proggi64/fischertechnik-box-foundation/Documentation/de/Base/getStrutDepth.md

# getStrutDepth

Funktion: Liefert die Breite einer Strebe.

## Use
```
use <../Base/Constants.scad>
```

## Syntax
```
getStrutDepth();
```

## Rückgabewert
Breite einer Strebe (8 mm).
