proggi64/fischertechnik-box-foundation/Documentation/de/Base/getStrutOuterTolerance.md

# getStrutOuterTolerance

Funktion: Liefert die Toleranz für Strebenhalter. Diese wird auf die Maße einer Strebe addiert, damit sie in die Halterungen passt. Durch Drucktoleranzen sind die Halterungen sonst zu eng und die Streben passen nicht hinein.

## Use
```
use <../Base/Constants.scad>
```

## Syntax
```
getStrutOuterTolerance();
```

## Rückgabewert
Toleranz für Strebenhalterungen (0,6 mm).
