proggi64/fischertechnik-box-foundation/Documentation/de/Base/getStrutThickness.md

# getStrutThickness

Funktion: Liefert die Dicke einer Strebe.

## Use
```
use <../Base/Constants.scad>
```

## Syntax
```
getStrutThickness();
```

## Rückgabewert
Stärke einer Strebe (2,8 mm).
