proggi64/fischertechnik-box-foundation/Documentation/de/Elements/CylinderHub.md

# CylinderHub

Nabe und Flachnabe.

- 31014
- 31015
- 31058
- 35030

CylinderHub

## Use
```
use <../Elements/CylinderHub.scad>
```

## Syntax
```
CylinderHub();

space = getCylinderHubSpace();
```

## Rückgabewert getCylinderHubSpace
Fläche als \[x,y]-Liste. Wenn auf der Nabe noch ein Bauteil (z.B. Zahnrad Z30) angebracht ist, sollte jeweils das dafür entworfene Element verwendet werden, damit die Fläche richtig dimensioniert ist.
