proggi64/fischertechnik-box-foundation/Documentation/de/Elements/CylinderLockingAxis30.md

# CylinderLockingAxis30
Rastachse 30 stehend.
- 35063

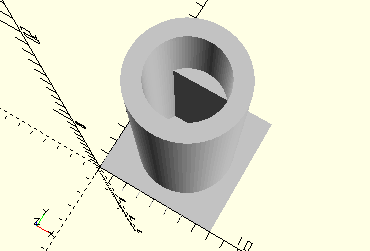
[picture p9: Documentation/images/CylinderLockingAxis30.png]
CylinderLockingAxis30


## Use
```
use <../Elements/CylinderLockingAxis30.scad>
```

## Syntax
```
CylinderLockingAxis30();

space = getCylinderLockingAxis30Space();
```

## Rückgabewert getCylinderLockingAxis30Space
Fläche als \[x,y]-Liste
