proggi64/fischertechnik-box-foundation/Documentation/de/Elements/CylinderLockingBevelGear.md

# CylinderLockingBevelGear
Rastachse mit Kegelzahnrad.
- 35061

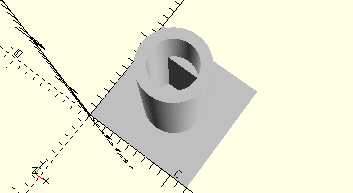
[picture p10: Documentation/images/CylinderLockingBevelGear.png]
CylinderLockingBevelGear


## Use
```
use <../Elements/CylinderLockingBevelGear.scad>
```

## Syntax
```
CylinderLockingBevelGear();

space = getCylinderLockingBevelGearSpace();
```

## Rückgabewert getCylinderLockingBevelGearSpace
Fläche als \[x,y]-Liste
