proggi64/fischertechnik-box-foundation/Documentation/de/Elements/Frame9VBatterySet.md

# Frame9VBatterySet
Batteriekasten für 9V-Block mit Polwendeschalter (wie im Motor Set XS).
- 135719

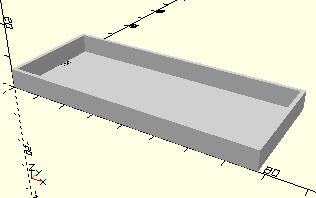
[picture p11: Documentation/images/Frame9VBatterySet.png]
Frame9VBatterySet


3D-Druck getestet.

## Use
```
use <../Elements/Frame9VBatterySet.scad>
```

## Syntax
```
Frame9VBatterySet();

space = getFrame9VBatterySetSpace();
```

## Rückgabewert getFrame9VBatterySetSpace
Fläche als \[x,y]-Liste
