proggi64/fischertechnik-box-foundation/Documentation/de/Elements/FrameUFormGearbox.md

# FrameUFormGearbox
U-Getriebe für Minimotor.
- 31068
- 31078

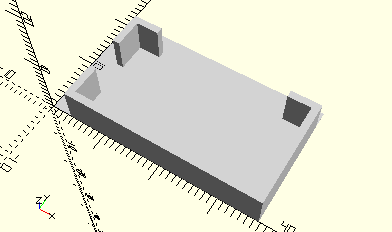
[picture p15: Documentation/images/FrameUFormGearbox.png]
FrameUFormGearbox


3D-Druck getestet.

## Use
```
use <../Elements/FrameUFormGearbox.scad>
```

## Syntax
```
FrameUFormGearbox();

space = getFrameUFormGearboxSpace();
```

## Rückgabewert getFrameUFormGearboxSpace
Fläche als \[x,y]-Liste
