proggi64/fischertechnik-box-foundation/Documentation/de/Elements/FrameAxis110.md

# FrameAxis110
Achse 110.
- 31031

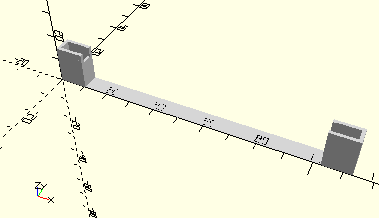
[picture p16: Documentation/images/FrameAxis110.png]
FrameAxis110


## Use
```
use <../Elements/FrameAxis110.scad>
```

## Syntax
```
FrameAxis110(count=1);

space = getFrameAxis110Space(count=1);
```

| Parameter | Typ | Beschreibung |
| --- | --- | --- |
| count | Integer | Anzahl der Achsen. |

## Rückgabewert getFrameAxis110Space
Fläche als \[x,y]-Liste
