proggi64/fischertechnik-box-foundation/Documentation/de/Elements/FrameAxis180.md

# FrameAxis180
Rastachse 180.
- 37527

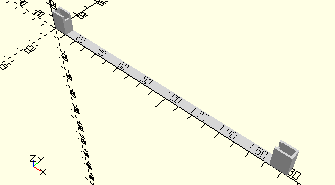
[picture p18: Documentation/images/FrameAxis180.png]
FrameAxis180


## Use
```
use <../Elements/FrameAxis180.scad>
```

## Syntax
```
FrameAxis180(
    count=1);

space = get$FrameAxis180Space(
    count=1);
```

| Parameter | Typ | Beschreibung |
| --- | --- | --- |
| count | Integer | Anzahl der Achsen. |

## Rückgabewert getFrameAxis180Space
Fläche als \[x,y]-Liste
