proggi64/fischertechnik-box-foundation/Documentation/de/Elements/FrameAxis30.md

# FrameAxis30

Achse 30 und Rastachse 30.

- 31034
- 35063

FrameAxis30

## Use
```
use <../Elements/FrameAxis30.scad>
```

## Syntax
```
FrameAxis30(count=1);

space = getFrameAxis30Space(count=1);
```

| Parameter | Typ | Beschreibung |
| --- | --- | --- |
| count | Integer | Anzahl der Achsen. |

## Rückgabewert getFrameAxis30Space
Äußere Fläche als \[x,y]-Liste.
