proggi64/fischertechnik-box-foundation/Documentation/de/Elements/FrameAxis40.md

# FrameAxis40
Achse 40 oder Kunststoffachse 40.
- 38314
- 38414

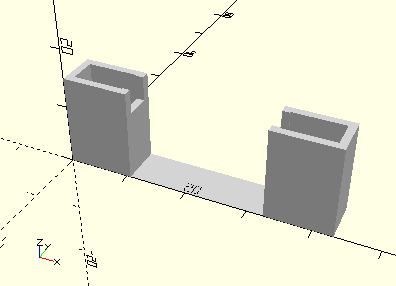
[picture p19: Documentation/images/FrameAxis40.png]
FrameAxis40


## Use
```
use <../Elements/FrameAxis40.scad>
```

## Syntax
```
FrameAxis40(count=1);

space = getFrameAxis40Space(count=1);
```

| Parameter | Typ | Beschreibung |
| --- | --- | --- |
| count | Integer | Anzahl der Achsen. |

## Rückgabewert getFrameAxis40Space
Fläche als \[x,y]-Liste
