proggi64/fischertechnik-box-foundation/Documentation/de/Elements/FrameAxis50.md

# FrameAxis50
Achse 50.
- 31033
- 38315 (alt, Kunststoffachse 50 grau)
- 38415

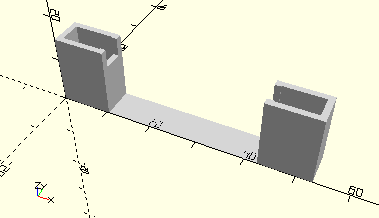
[picture p20: Documentation/images/FrameAxis50.png]
FrameAxis50


## Use
```
use <../Elements/FrameAxis50.scad>
```

## Syntax
```
FrameAxis50(count=1);

space = getFrameAxis50Space(count=1);
```

| Parameter | Typ | Beschreibung |
| --- | --- | --- |
| count | Integer | Anzahl der Achsen. |

## Rückgabewert getFrameAxis50Space
Fläche als \[x,y]-Liste
