proggi64/fischertechnik-box-foundation/Documentation/de/Elements/FrameAxis80.md

# FrameAxis80
Achse 80.
- 37384

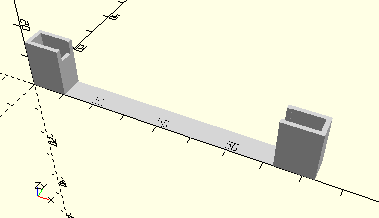
[picture p23: Documentation/images/FrameAxis80.png]
FrameAxis80


## Use
```
use <../Elements/FrameAxis80.scad>
```

## Syntax
```
FrameAxis80(count=1);

space = getFrameAxis80Space(count=1);
```

| Parameter | Typ | Beschreibung |
| --- | --- | --- |
| count | Integer | Anzahl der Achsen. |

## Rückgabewert getFrameAxis80Space
Fläche als \[x,y]-Liste
