proggi64/fischertechnik-box-foundation/Documentation/de/Elements/FrameAxis90.md

# FrameAxis90
Achse 90.
- 31040

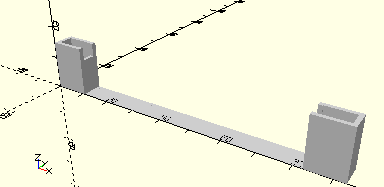
[picture p24: Documentation/images/FrameAxis90.png]
FrameAxis90


## Use
```
use <../Elements/FrameAxis90.scad>
```

## Syntax
```
FrameAxis90(count=1);

space = getFrameAxis90Space(count=1);
```

| Parameter | Typ | Beschreibung |
| --- | --- | --- |
| count | Integer | Anzahl der Achsen. |

## Rückgabewert getFrameAxis90Space
Fläche als \[x,y]-Liste
