proggi64/fischertechnik-box-foundation/Documentation/de/Elements/FrameCrankedAxis.md

# FrameCrankedAxis
Kurbelwelle.
- 31080

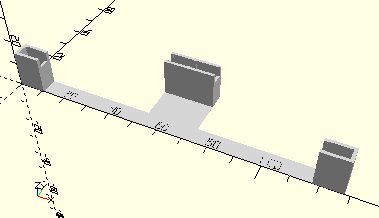
[picture p27: Documentation/images/FrameCrankedAxis.png]
FrameCrankedAxis


3D-Druck getestet.

## Use
```
use <../Elements/FrameCrankedAxis.scad>
```

## Syntax
```
FrameCrankedAxis();

space = getFrameCrankedAxisSpace();
```

## Rückgabewert getFrameCrankedAxisSpace
Fläche als \[x,y]-Liste. Diese Fläche ist das gesamte Rechteck, auch wenn die linke und rechte obere Ecke nicht von der Achse belegt sind.
