proggi64/fischertechnik-box-foundation/Documentation/de/Elements/FrameUniversalJointCardan.md

# FrameUniversalJointCardan
Kardangelenk mit zwei Spannzangen.
- 31044
- 35113

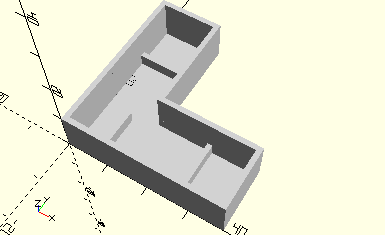
[picture p28: Documentation/images/FrameUniversalJointCardan.png]
FrameUniversalJointCardan


Das Element ist vorgesehen für eine Kardangelenk, das mit zwei Spannzangen (35113) montiert ist.

3D-Druck getestet.

## Use
```
use <../Elements/FrameUniversalJointCardan.scad>
```

## Syntax
```
FrameUniversalJointCardan();

space = getFrameUniversalJointCardanSpace();
```

## Rückgabewert getFrameUniversalJointCardanSpace
Fläche als \[x,y]-Liste. Gerechnet werden die beiden langen Seiten für x und y.
