proggi64/fischertechnik-box-foundation/Documentation/de/Elements/CylinderAndAxisSegmentDisc.md

# CylinderAndAxisSegmentDisc
Segmentscheibe.
- 31037

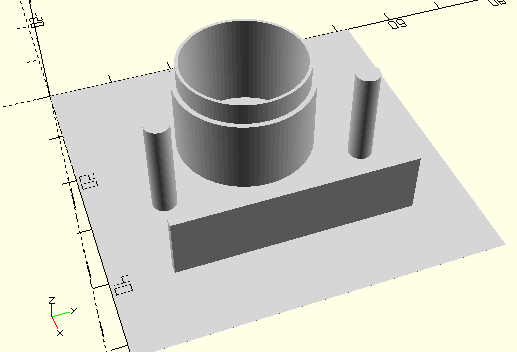
[picture p29: Documentation/images/CylinderAndAxisSegmentDisc.png]
CylinderAndAxisSegmentDisc


3D-Druck getestet

## Use
```
use <../Elements/CylinderAndAxisSegmentDisc.scad>
```

## Syntax
```
CylinderAndAxisSegmentDisc();

space = getCylinderAndAxisSegmentDiscSpace();
```

## Rückgabewert getCylinderAndAxisSegmentDiscSpace
Fläche als \[x,y]-Liste
