proggi64/fischertechnik-box-foundation/Documentation/de/Base/getHubRingLevelDiameter.md

# getHubRingLevelDiameter

Funktion: Liefert den äußeren Durchmesser für die dickere Basis, auf den ein Rad oder Reifen für eine Nabe passt.

__getHubRingLevelDiameter__ wird durchgängig im Framework für alle Zylinder verwendet, auf die der innere Ring von Rädern passen soll, die auf eine Nabe gesetzt werden.

## Use
```
use <../Base/Constants.scad>
```

## Syntax
```
getHubRingLevelDiameter();
```

## Rückgabewert
Äußerer Durchmesser der dickeren Basis eines Rings, auf den Räder gesteckt weren können, die mit einer Nabe verbunden werden sollen. Beispiel: [CylinderGearZ20](../Elements/CylinderGearZ20.md).
