proggi64/fischertechnik-box-foundation/Documentation/de/Base/getPropellerAxisDiameter.md

# getPropellerAxisDiameter

Funktion: Liefert den äußeren Durchmesser der Achse einer Propellerspitze.

## Use
```
use <../Base/Constants.scad>
```

## Syntax
```
getPropellerAxisDiameter();
```

## Rückgabewert
Durchmesser der Achse einer Propellerspitze.
