proggi64/fischertechnik-box-foundation/Documentation/de/Base/getPropellerAxisTolerance.md

# getPropellerAxisTolerance

Funktion: Liefert die Drucktoleranz für den äußeren Durchmesser der Achse einer Propellerspitze. Diese Toleranze sollte bei gedruckten Achsen vom Duchmesser abgezogen werden, damit der Propeller auf die Achse passt. Durch Ungenauigkeiten beim Druck kann es sonst dazu kommen, dass der propeller nicht passt.

## Use
```
use <../Base/Constants.scad>
```

## Syntax
```
getPropellerAxisDiameter();
```

## Rückgabewert
Drucktoleranz für den äußeren Durchmesser der Achse einer Propellerspitze.
