proggi64/fischertechnik-box-foundation/Documentation/de/Base/getStrutEndRadius.md

# getStrutEndRadius

Funktion: Liefert den Radius vom Schraubenloch zum Rand einer Strebe.

## Use
```
use <../Base/Constants.scad>
```

## Syntax
```
getStrutEndRadius();
```

## Rückgabewert
Radius vom Schraubenloch zum Rand einer Strebe. Der Wert wird benötigt, um die Gesamtlänge einer Strebe aus der Nominallänge zu errechnen (siehe [__getFullStrutLength__](getFullStrutLength.md)). Er beträgt 4,5 mm.
