proggi64/fischertechnik-box-foundation/Documentation/de/Elements/AxisPropellerTip.md

# AxisPropellerTip
Propellerspitze.
- 37681

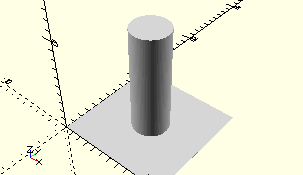
[picture p38: Documentation/images/AxisPropellerTip.png]
AxisPropellerTip


## Use
```
use <../Elements/AxisPropellerTip.scad>
```

## Syntax
```
AxisPropellerTip();

space = getAxisPropellerTipSpace();
```

## Rückgabewert getAxisPropellerTipSpace
Fläche als \[x,y]-Liste
