proggi64/fischertechnik-box-foundation/Documentation/de/Base/getPinHeight.md

# getStudHeight

Funktion: Liefert die Länge eines Baustein-Verbindingszapfens.

## Use
```
use <../Base/Deployment.scad>
```

## Syntax
```
getStudHeight();
```

## Rückgabewert
Liefert die Länge eines Verbindingszapfens. Die Zapfen sind 2,5 mm lang. zusätzlich sollte immer noch [__getStudTolerance__](getStudTolerance.md) auf diesen Wert addiert werden.
