proggi64/fischertechnik-box-foundation/Documentation/de/Base/getPinTolerance.md

# getStudTolerance

Funktion: Liefert die zusätzliche Toleranz, wenn Abstände für Baustein-Verbindingszapfen erzeugt werden.

## Use
```
use <../Base/Deployment.scad>
```

## Syntax
```
getStudTolerance();
```

## Rückgabewert
Die zusätzliche Toleranz für Platz, den die Verbindingszapfen in Elementen benötigen. Die Zapfen sind 2,5 mm, die Toleranz wird auf diesen Wert addiert.
