proggi64/fischertechnik-box-foundation/Documentation/de/Elements/FrameBlock5TwoStuds.md

# FrameBlock5TwoStuds
Baustein 5 mit zwei Zapfen.
- 37238

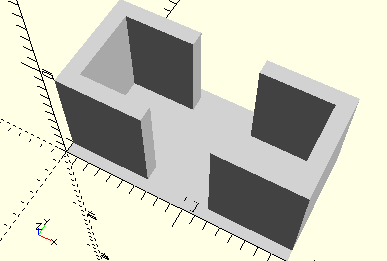
[picture p40: Documentation/images/FrameBlock5TwoStuds.png]
FrameBlock5TwoStuds


## Use
```
use <../Elements/FrameBlock5TwoStuds.scad>
```

## Syntax
```
FrameBlock5TwoStuds(
    count=1);

space = get$FrameBlock5TwoStudsSpace(
    count=1);
```

| Parameter | Typ | Beschreibung |
| --- | --- | --- |
| count | Integer | Anzahl der Bausteine nebeneinander |

## Rückgabewert getFrameBlock5TwoStudsSpace
Fläche als \[x,y]-Liste

## Beispiel

```
use <../../Elements/FrameBlock5TwoStuds.scad>

count=3;
FrameBlock5TwoStuds(count);
```

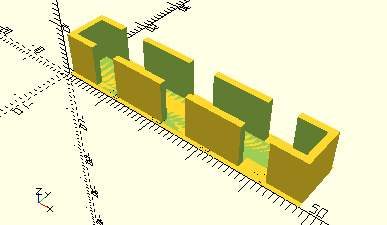
[picture p41: Documentation/images/TestFrameBlock5TwoStuds_3.png]
3 Bausteine
