proggi64/fischertechnik-box-foundation/Documentation/de/ModelBase/ElevatedFramesWithCutoff.md

# ElevatedFramesWithCutoff

Erzeugt eine Halterung, die im Normalfall für einzelne Achsen verwendet wird.

TestFrameAxis50

Die Halterung besteht aus zwei Rahmen an den Enden, jeweils mit einer Aussparung für das jeweilige Ende des Bauteils. Die Aussparung ist in der Standardeinstellung durch eine Wand abgeschlossen. Über Parameter können diese Abschlusswände auch weggelassen werden. Das Modul __ElevatedFramesWithCutoff__ wird vom ModelBase-Modul [__FrameAxis__](FrameAxis.md) verwendet. __FrameAxis__ verwendet für einige der hier aufgeführten Parameter Standardwerte, u.a. die Achsdurchmesser und eine konstante Höhe der Halterungen.

## Use
```
use <../ModelBase/Complex.scad>
```

## Syntax
```
ElevatedFramesWithCutoff(
  volume, 
  depth,
  height, 
  bearingLength, 
  cutThrough=false,
  clampThrough=false,
  single=false);
```

| Parameter | Typ | Beschreibung |
| --- | --- | --- |
| volume | \[x,y,z] | Volumen des Bauelements, welches in dem Rahmen passen soll. Für eine Achse ist dies die Achslänge als X-Wert, und der Durchmesser für Tiefe und Höhe. |
| depth | Decimal | Jeweilige Tiefe der beiden Halterungsrahmen. Der Ausschnitt wird dann mittig in der notwendigen Breite für *volume.y* gesetzt. *depth* gibt also an, wie viel noch neben dem Ausschnitt an Wandlänge stehen bleibt und sollte ein wenig mehr als den Achsdurchmesser betragen. |
| height | Decimal | Jeweilige Höhe der beiden Halterungsrahmen. |
| bearingLength | Decimal | Jeweilige Länge der beiden Halterungsrahmen. Bei Achsen sollte diese weniger als die Hälfte der Achslänge betragen. |
| cutThrough | Boolean | __true__, wenn die Wand am Ende der beiden Halterungen weggelassen werden soll. |
| clampThrough | Boolean | __true__, wenn die komplette Wand am etwas engeren Einlass der Achse bis zum Boden entfernt werden soll. Das wird intern vom Modul [__AxisMiddleSupport__](AxisMiddleSupport.md) verwendet. |
| single | Boolean | __true__, wenn nur ein Halter für die linke Seite erzeugt werden soll. |

## Beispiele

### Breite und Höhe der Auflage individuell angeben
```
use <../../Base/Constants.scad>
use <../../ModelBase/Complex.scad>

ElevatedFramesWithCutoff([40, 20, 15], depth=20, height=20, bearingLength=10);
```

ElevatedFramesWithCutoff

### Wand bis zum Boden entfernen
```
use <../../Base/Constants.scad>
use <../../ModelBase/Complex.scad>

ElevatedFramesWithCutoff([9, 4, 4], 5, 10, 4, cutThrough=true, single=true, clampThrough=true);
```

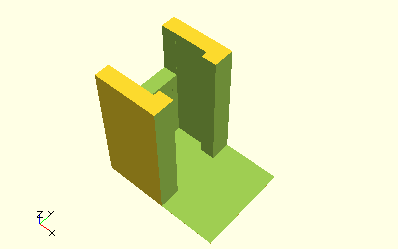
[picture p42: Documentation/images/ElevatedFramesWithCutoff_2.png]
Wand bis zum Boden entfernt


### Mittlere Halterung
```
use <../../Base/Constants.scad>
use <../../ModelBase/Complex.scad>

ElevatedFramesWithCutoff([9, 4, 4], 5, 10, 4, cutThrough=true, single=false, clampThrough=true);
```

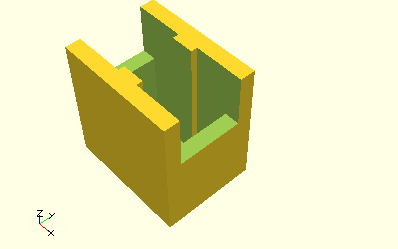
[picture p43: Documentation/images/ElevatedFramesWithCutoff_3.png]
Mittelhalterung
