proggi64/fischertechnik-box-foundation/Documentation/de/Elements/FrameAngleEquilateral.md

# FrameAngleEquilateral

Winkelstein 60 gleichseitig.

- 31010

## Use
```
use <../Elements/FrameAngleEquilateral.scad>
```

## Syntax
```
FrameAngleEquilateral(
    count=1);

space = getFrameAngleEquilateralSpace()
    count=1);
```

| Parameter | Typ | Beschreibung |
| --- | --- | --- |
| count | Integer | Anzahl der Bausteine nebeneinander (X-Richtung). |

## Rückgabewert getFrameAngleEquilateralSpace
Äußere Fläche des Rahmens als \[x,y]-Liste.
