proggi64/fischertechnik-box-foundation/Documentation/de/Elements/FrameAngle15.md

# FrameAngle15
Winkelstein 15° hochkant.
- 31981

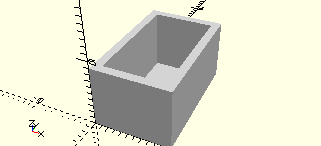
[picture p44: Documentation/images/FrameAngle15.png]
FrameAngle15


## Use
```
use <../Elements/FrameAngle15.scad>
```

## Syntax
```
FrameAngle15(
    count=1);

space = getFrameAngle15Space(
    count=1);
```

| Parameter | Typ | Beschreibung |
| --- | --- | --- |
| count | Integer | Anzahl der Bausteine nebeneinander (X-Richtung). |

## Rückgabewert getFrameAngle15Space
Fläche als \[x,y]-Liste
