proggi64/fischertechnik-box-foundation/Documentation/de/Elements/FrameAngle7p5.md

# FrameAngle7p5
Winkelstein 7,5° hochkant.
- 32071

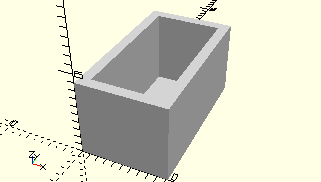
[picture p45: Documentation/images/FrameAngle7p5.png]
FrameAngle7p5


## Use
```
use <../Elements/FrameAngle7p5.scad>
```

## Syntax
```
FrameAngle7p5(
    count=1);

space = getFrameAngle7p5Space(
    count=1);
```

| Parameter | Typ | Beschreibung |
| --- | --- | --- |
| count | Integer | Anzahl der Bausteine nebeneinander (X-Richtung). |

## Rückgabewert getFrameAngle7p5Space
Fläche als \[x,y]-Liste
