proggi64/fischertechnik-box-foundation/Documentation/de/Elements/FrameBlock15x30x5.md

# FrameBlock15x30x5
Baustein 15x30x5 mit einem Zapfen.
- 35049

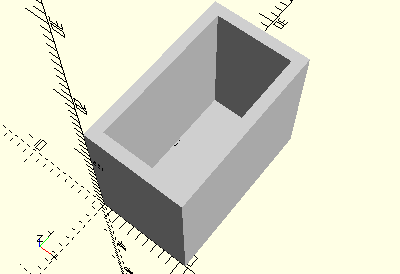
[picture p46: Documentation/images/FrameBlock15x30x5.png]
FrameBlock15x30x5


## Use
```
use <../Elements/FrameBlock15x30x5.scad>
```

## Syntax
```
FrameBlock15x30x5(
    columns=1, 
    rows=1);

space = getFrameBlock15x30x5Space(
    columns=1, 
    rows=1);
```

| Parameter | Typ | Beschreibung |
| --- | --- | --- |
| columns | Integer | Anzahl der Bausteine nebeneinander (X-Richtung). |
| rows | Integer | Anzahl der Bausteine untereinander (Y-Richtung). |

## Rückgabewert getFrameBlock15x30x5Space
Fläche als \[x,y]-Liste
