proggi64/fischertechnik-box-foundation/Documentation/de/Elements/FrameTransistorBlock.md

# FrameTransistorBlock
Montierter Transistorbaustein aus PROFI Electronics (Transistor BC 547 C).
- 152059
- 152218
- 152860

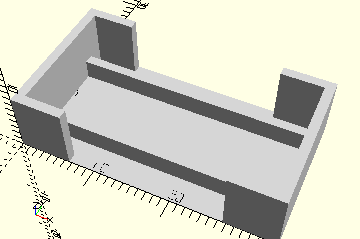
[picture p47: Documentation/images/FrameTransistorBlock.png]
FrameTransistorBlock


## Use
```
use <../Elements/FrameTransistorBlock.scad>
```

## Syntax
```
FrameTransistorBlock();

space = getFrameTransistorBlockSpace();
```

## Rückgabewert getFrameTransistorBlockSpace
Fläche als \[x,y]-Liste
