proggi64/fischertechnik-box-foundation/Documentation/de/Elements/FramePlasticBall20.md

# FramePlasticBall20
Plastikkugel 20mm wie in ROBOTICS SmartTech.
- 185695

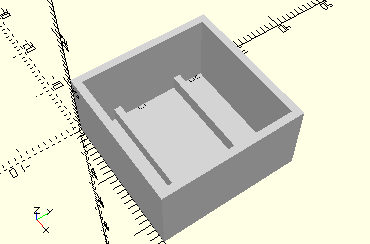
[picture p52: Documentation/images/FramePlasticBall20.png]
FramePlasticBall20


## Use
```
use <../Elements/FramePlasticBall20.scad>
```

## Syntax
```
FramePlasticBall20(
    count=1);

space = get$FramePlasticBall20Space(
    count=1);
```

| Parameter | Typ | Beschreibung |
| --- | --- | --- |
| count | Integer | Zahl der Kugeln nebeneinander. |

## Rückgabewert getFramePlasticBall20Space
Fläche als \[x,y]-Liste
