proggi64/fischertechnik-box-foundation/Documentation/de/Elements/FrameReedRelayHolder.md

# FrameReedRelayHolder
Reed-Kontakt Halter.
- 35969

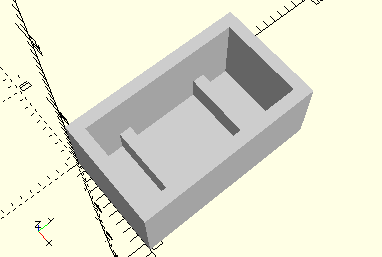
[picture p53: Documentation/images/FrameReedRelayHolder.png]
FrameReedRelayHolder


## Use
```
use <../Elements/FrameReedRelayHolder.scad>
```

## Syntax
```
FrameReedRelayHolder();

space = getFrameReedRelayHolderSpace();
```

## Rückgabewert getFrameReedRelayHolderSpace
Fläche als \[x,y]-Liste
