proggi64/fischertechnik-box-foundation/Documentation/de/Elements/FrameMiniPushButton.md

# FrameMiniPushButton
Minitaster.
- 37780
- 37783

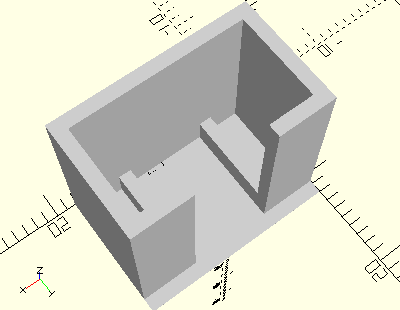
[picture p54: Documentation/images/FrameMiniPushButton.png]
FrameMiniPushButton


## Use
```
use <../Elements/FrameMiniPushButton.scad>
```

## Syntax
```
FrameMiniPushButton();

space = getFrameMiniPushButtonSpace();
```

## Rückgabewert getFrameMiniPushButtonSpace
Fläche als \[x,y]-Liste
