proggi64/fischertechnik-box-foundation/Documentation/de/Elements/FrameTrailSensor.md

# FrameTrailSensor
Spursensor mit Kabeln.
- 128598

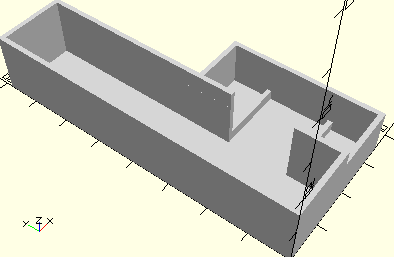
[picture p55: Documentation/images/FrameTrailSensor.png]
FrameTrailSensor


Für die montierten Kabel ist eine Box mit Kabeldurchlass angebracht.

## Use
```
use <../Elements/FrameTrailSensor.scad>
```

## Syntax
```
FrameTrailSensor();

space = getFrameTrailSensorSpace();
```

## Rückgabewert getFrameTrailSensorSpace
Fläche als \[x,y]-Liste
