proggi64/fischertechnik-box-foundation/Documentation/de/Elements/Frame9VMiniMotor.md

# Frame9VMiniMotor
Mini-Motor 9V.
- 32293

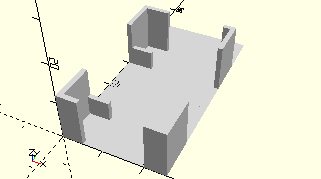
[picture p57: Documentation/images/Frame9VMiniMotor.png]
Frame9VMiniMotor


Auf der Seite liegend, Anschlüsse links.

## Use
```
use <../Elements/Frame9VMiniMotor.scad>
```

## Syntax
```
Frame9VMiniMotor();

space = getFrame9VMiniMotorSpace();
```

## Rückgabewert getFrame9VMiniMotorSpace
Fläche als \[x,y]-Liste
