proggi64/fischertechnik-box-foundation/Documentation/de/Elements/FrameSidePiece15.md

# FrameSidePiece15
Verlängerung Seitenteil 15 mm.
- 163200

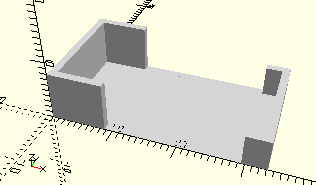
[picture p58: Documentation/images/FrameSidePiece15.png]
FrameSidePiece15


## Use
```
use <../Elements/FrameSidePiece15.scad>
```

## Syntax
```
FrameSidePiece15(
    count=1);

space = get$FrameSidePiece15Space(
    count=1);
```

| Parameter | Typ | Beschreibung |
| --- | --- | --- |
| count | Integer | Anzahl der nebeneinander liegenden Seitenteile. |

## Rückgabewert getFrameSidePiece15Space
Fläche als \[x,y]-Liste
