proggi64/fischertechnik-box-foundation/Documentation/de/Elements/FrameSidePieceLeft.md

# FrameSidePieceLeft
Linkes Seitenteil.
- 163198

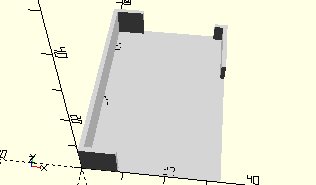
[picture p59: Documentation/images/FrameSidePieceLeft.png]
FrameSidePieceLeft


## Use
```
use <../Elements/FrameSidePieceLeft.scad>
```

## Syntax
```
FrameSidePieceLeft();

space = getFrameSidePieceLeftSpace();
```

## Rückgabewert getFrameSidePieceLeftSpace
Fläche als \[x,y]-Liste
