proggi64/fischertechnik-box-foundation/Documentation/de/Elements/FrameSidePieceRight.md

# FrameSidePieceRight
Rechtes Seitenteil.
- 163199

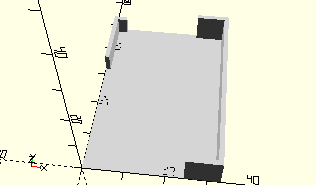
[picture p60: Documentation/images/FrameSidePieceRight.png]
FrameSidePieceRight


## Use
```
use <../Elements/FrameSidePieceRight.scad>
```

## Syntax
```
FrameSidePieceRight();

space = getFrameSidePieceRightSpace();
```

## Rückgabewert getFrameSidePieceRightSpace
Fläche als \[x,y]-Liste
