proggi64/fischertechnik-box-foundation/Documentation/de/Elements/CylinderOmniWheel.md

# CylinderOmniWheel
Montiertes Omniwheel.
- 183025
- 183026
- 183027
- 183028

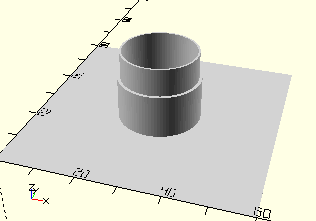
[picture p61: Documentation/images/CylinderOmniWheel.png]
CylinderOmniWheel


## Use
```
use <../Elements/CylinderOmniWheel.scad>
```

## Syntax
```
CylinderOmniWheel();

space = getCylinderOmniWheelSpace();
```

## Rückgabewert getCylinderOmniWheelSpace
Fläche als \[x,y]-Liste
