proggi64/fischertechnik-box-foundation/Documentation/de/ModelBase/Divider.md

# Divider

Erzeugt einen Trenner innerhalb eines Sortierkastens. Der Trenner reicht immer von Wand zu Wand. Die Ausrichtung und die Position wird über die Parameter *align* und *distance* angegeben.

DockedFrame

Die Trennwand verschmilzt mit den beiden Außenwänden.

## Use
```
use <../ModelBase/Simple.scad>
include <../Base/PlacementOptions.scad>
```

## Syntax
```
Divider(
  distance, 
  align=AlignLeft, 
  height=getSmallPartsFrameHeight(), 
  boxSpace=getBox190Space());
```

| Parameter | Typ | Beschreibung |
| --- | --- | --- |
| distance | Decimal | Innerer Abstand zwischen Außenwand und Trennwand, gerechnet von der durch *align* festgelegten Wand. |
| align | Integer (Enum) |  Legt die Ausrichtung fest und von welcher Wand aus *distance* gerechnet wird. Mögliche Werte: __AlignLeft__, __AlignRight__, __AlignBottom__ oder __AlignTop__. |
| height | Decimal | Höhe der Trennwand. Standard ist 10 mm ([__getSmallPartsFrameHeight__](getSmallPartsFrameHeight.md)). |
| boxSpace | \[x,y] | Fläche des Sortierkastens, in dem der Trenner gesetzt werden soll. Standard ist die Box 190x130. |

## Beispiele

## Trennwand relativ zur linken Wand
```
use <../ModelBase/Simple.scad>
include <../Base/PlacementOptions.scad>

#Box190();
Divider(15);
```
Setzt eine Trennwand in 15 mm Entfernung von der linken Wand.

Divider_1

## Trennwand relativ zur oberen Wand
```
use <../ModelBase/Simple.scad>
include <../Base/PlacementOptions.scad>

#Box190();
Divider(15, alignTop);
```
Setzt eine Trennwand in 15 mm Entfernung von der oberen Wand.

Divider_2
