proggi64/fischertechnik-box-foundation/Documentation/de/ModelBase/FrameLeftCutoff.md

# FrameLeftCutoff

Erzeugt einen Kubus, der mit __difference__ einen Ausschnitt in der linken Wand eines mit [__Frame__](Frame.md) erzeugten Rahmens schneidet.

## Use
```
use <../ModelBase/Simple.scad>
```

## Syntax
```
FrameLeftCutoff(
  volume,
  width,
  offset=0,
  tolerance=getTolerance());
```

| Parameter | Typ | Beschreibung |
| --- | --- | --- |
| volume | \[x,y,z] | Länge x Breite x Höhe des Inneraums. Auf Länge und Breite wird noch der Wert von *tolerance* für das tatsächliche innere Volumen gerechnet. |
| width | Decimal | Breite des Ausschnitts. |
| offset | Decimal | Y-Offset des Ausschnitts. Positive Werte verschieben nach hinten, negative nach vorne. |
| tolerance | Decimal | Toleranzwert, der zu Länge und Breite gerechnet wird, damit in das gedruckte Element das Bauteil hineinpasst. Standard ist [__getTolerance()__](../Base/getTolerance.md). Wenn der Rahmen exakt den Angaben in *volume* entsprechen soll, muss hier 0 angegeben werden. |

## Beispiel

```
cutoffWidth = 3;
offset = -1;

difference() {
    Frame([10,10,10]);
    FrameLeftCutoff([10,10,10], cutoffWidth, offset);
}
```

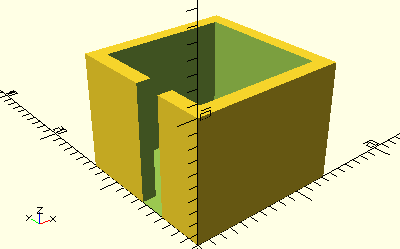
[picture p67: Documentation/images/SimpleTestFrameLeftCutoff_1.png]
Mit offset
