proggi64/fischertechnik-box-foundation/Documentation/de/Elements/HolderLiftingJoint.md

# HolderLiftingJoint
Hubgelenk für Mini-Motor Hubstange.
- 37282

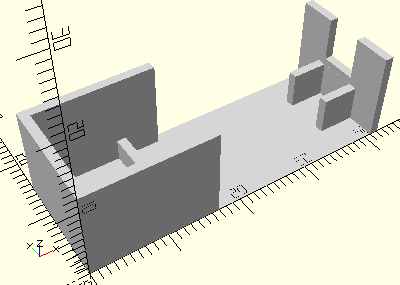
[picture p71: Documentation/images/HolderLiftingJoint.png]
HolderLiftingJoint


## Use
```
use <../Elements/HolderLiftingJoint.scad>
```

## Syntax
```
HolderLiftingJoint();

space = getHolderLiftingJointSpace();
```

## Rückgabewert getHolderLiftingJointSpace
Fläche als \[x,y]-Liste
