proggi64/fischertechnik-box-foundation/Documentation/de/Elements/FrameSwivelBaseForMiniMotor.md

# FrameSwivelBaseForMiniMotor
Drehschieber für Mini-Motor.
- 31070

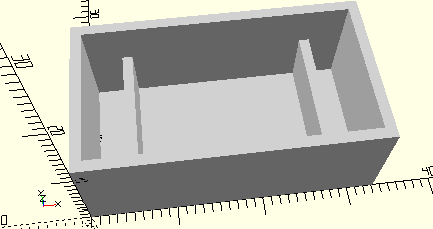
[picture p72: Documentation/images/FrameSwivelBaseForMiniMotor.png]
FrameSwivelBaseForMiniMotor


## Use
```
use <../Elements/FrameSwivelBaseForMiniMotor.scad>
```

## Syntax
```
FrameSwivelBaseForMiniMotor();

space = getFrameSwivelBaseForMiniMotorSpace();
```

## Rückgabewert getFrameSwivelBaseForMiniMotorSpace
Fläche als \[x,y]-Liste
