proggi64/fischertechnik-box-foundation/Documentation/de/Elements/FrameGearBlockWithWorm.md

# FrameGearBlockWithWorm
Getriebeblock mit Schnecke m 1,5 für Mini-Motor (wie in mini-mot 1).
- 31066
- 31075

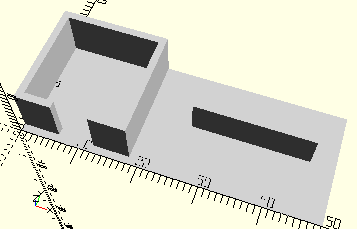
[picture p73: Documentation/images/FrameGearBlockWithWorm.png]
FrameGearBlockWithWorm


## Use
```
use <../Elements/FrameGearBlockWithWorm.scad>
```

## Syntax
```
FrameGearBlockWithWorm();

space = getFrameGearBlockWithWormSpace();
```

## Rückgabewert getFrameGearBlockWithWormSpace
Fläche als \[x,y]-Liste
