proggi64/fischertechnik-box-foundation/Documentation/de/Elements/CylinderClipContact.md

# CylinderClipContact
Klemmkontakt (wie in mini-mot 1).
- 31338

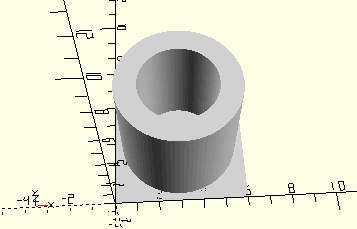
[picture p74: Documentation/images/CylinderClipContact.png]
CylinderClipContact


## Use
```
use <../Elements/CylinderClipContact.scad>
```

## Syntax
```
CylinderClipContact();

space = getCylinderClipContactSpace();
```

## Rückgabewert getCylinderClipContactSpace
Fläche als \[x,y]-Liste
