proggi64/fischertechnik-box-foundation/Documentation/de/Elements/FrameGearBlock.md

# FrameGearBlock
Getriebeblock für den Mini-Motor (wie mini-mot 1).
- 31067

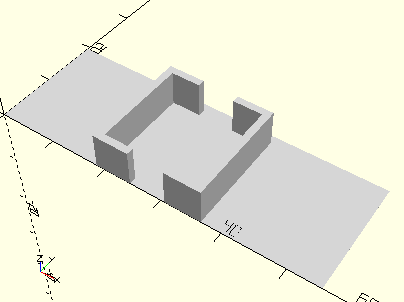
[picture p75: Documentation/images/FrameGearBlock.png]
FrameGearBlock


## Use
```
use <../Elements/FrameGearBlock.scad>
```

## Syntax
```
FrameGearBlock();

space = getFrameGearBlockSpace();
```

## Rückgabewert getFrameGearBlockSpace
Fläche als \[x,y]-Liste
