proggi64/fischertechnik-box-foundation/Documentation/de/Elements/FrameConnectingRod30.md

# FrameConnectingRod30
Schubstange 30 für Hubgetriebe.
- 37276

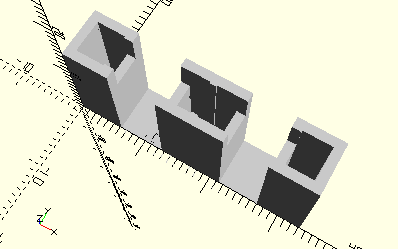
[picture p76: Documentation/images/FrameConnectingRod30.png]
FrameConnectingRod30


## Use
```
use <../Elements/FrameConnectingRod30.scad>
```

## Syntax
```
FrameConnectingRod30();

space = getFrameConnectingRod30Space();
```

## Rückgabewert getFrameConnectingRod30Space
Fläche als \[x,y]-Liste
