proggi64/fischertechnik-box-foundation/Documentation/de/Elements/FrameConnectingRod60.md

# FrameConnectingRod60
Schubstange 60 für Hubgetriebe.
- 37283

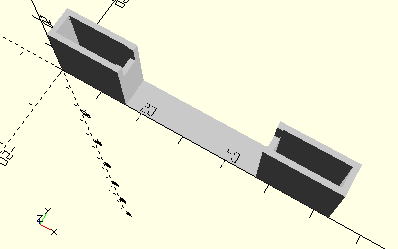
[picture p77: Documentation/images/FrameConnectingRod60.png]
FrameConnectingRod60


## Use
```
use <../Elements/FrameConnectingRod60.scad>
```

## Syntax
```
FrameConnectingRod60();

space = getFrameConnectingRod60Space();
```

## Rückgabewert getFrameConnectingRod60Space
Fläche als \[x,y]-Liste
