proggi64/fischertechnik-box-foundation/Documentation/de/Elements/FrameAxis40WithGearwheelZ28.md

# FrameAxis40WithGearwheelZ28
Achse 40 mit Zahnrad Z 28 für Minimotor-Getriebe.
- 31064

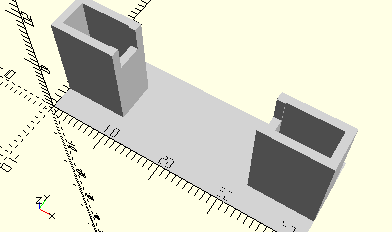
[picture p79: Documentation/images/FrameAxis40WithGearWheelZ28.png]
FrameAxis40WithGearwheelZ28


## Use
```
use <../Elements/FrameAxis40WithGearwheelZ28.scad>
```

## Syntax
```
FrameAxis40WithGearwheelZ28();

space = getFrameAxis40WithGearwheelZ28Space();
```

## Rückgabewert getFrameAxis40WithGearwheelZ28Space
Fläche als \[x,y]-Liste
