proggi64/fischertechnik-box-foundation/Documentation/de/Elements/FrameLiftingGear.md

# FrameLiftingGear
Hubgetriebe oder Hubgetrieberahmen ohne Zahnräder.
- 37263
- 37268
- 37272
- 75067

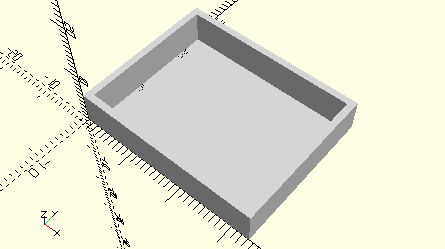
[picture p80: Documentation/images/FrameLiftingGear.png]
FrameLiftingGear


## Use
```
use <../Elements/FrameLiftingGear.scad>
```

## Syntax
```
FrameLiftingGear();

space = getFrameLiftingGearSpace();
```

## Rückgabewert getFrameLiftingGearSpace
Fläche als \[x,y]-Liste
