proggi64/fischertechnik-box-foundation/Documentation/de/Base/getHubRingDiameter.md

# getHubRingDiameter

Funktion: Liefert den äußeren Durchmesser des Rings, auf den ein Rad oder Reifen für eine Nabe passt.

__getHubRingDiameter__ wird durchgängig im Framework für alle Zylinder verwendet, auf die der innere Ring von Rädern passen soll, die auf eine Nabe gesetzt werden.

## Use
```
use <../Base/Constants.scad>
```

## Syntax
```
getHubRingDiameter();
```

## Rückgabewert
Äußerer Durchmesser eines Rings, auf den Räder gesteckt werden können, die mit einer Nabe verbunden werden sollen. Beispiel: [CylinderGearZ20](../Elements/CylinderGearZ20.md).
