proggi64/fischertechnik-box-foundation/Documentation/de/Elements/CylinderLargePulleyWheel.md

# CylinderLargePulleyWheel
Drehscheibe.
- 31019

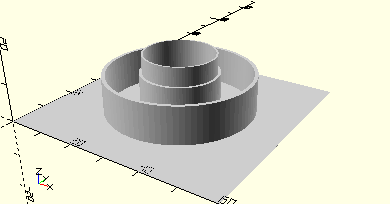
[picture p87: Documentation/images/CylinderLargePulleyWheel.png]
CylinderLargePulleyWheel


Drehscheibe ohne Nabe.

## Use
```
use <../Elements/CylinderLargePulleyWheel.scad>
```

## Syntax
```
CylinderLargePulleyWheel();

space = getCylinderLargePulleyWheelSpace();
```

## Rückgabewert getCylinderLargePulleyWheelSpace
Fläche als \[x,y]-Liste
