proggi64/fischertechnik-box-foundation/Documentation/de/Elements/FrameConcaveMirror.md

# FrameConcaveMirror
Hohlspiegel.
- 31369

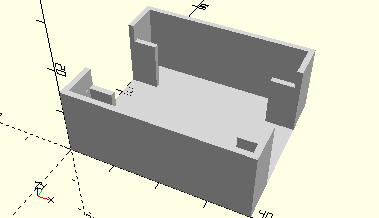
[picture p88: Documentation/images/FrameConcaveMirror.png]
FrameConcaveMirror


3D-Druck getestet

## Use
```
use <../Elements/FrameConcaveMirror.scad>
```

## Syntax
```
FrameConcaveMirror();

space = getFrameConcaveMirrorSpace();
```

## Rückgabewert getFrameConcaveMirrorSpace
Fläche als \[x,y]-Liste
