proggi64/fischertechnik-box-foundation/Documentation/de/Elements/FrameControlLight.md

# FrameControlLight
Elektronikbaustein Stecklampe 6V.
- 36390

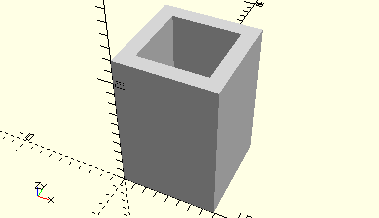
[picture p89: Documentation/images/FrameControlLight.png]
FrameControlLight


3D-Druck getestet

## Use
```
use <../Elements/FrameControlLight.scad>
```

## Syntax
```
FrameControlLight();

space = getFrameControlLightSpace();
```

## Rückgabewert getFrameControlLightSpace
Fläche als \[x,y]-Liste
