proggi64/fischertechnik-box-foundation/Documentation/de/Elements/FrameAngleRight.md

# FrameAngleRight
Rechtwikliger Winkelstein.
- 31012

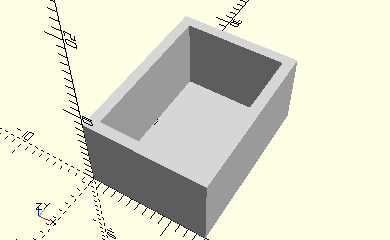
[picture p90: Documentation/images/FrameAngleRight.png]
FrameAngleRight


## Use
```
use <../Elements/FrameAngleRight.scad>
```

## Syntax
```
FrameAngleRight(
    count);

space = getFrameAngleRightSpace(
    count);
```

| Parameter | Typ | Beschreibung |
| --- | --- | --- |
| count | Integer | Anzahl der Winkelsteine. |

## Rückgabewert getFrameAngleRightSpace
Fläche als \[x,y]-Liste
