proggi64/fischertechnik-box-foundation/Documentation/de/Elements/CylinderAxis30.md

# CylinderAxis30
Halterung für stehende Achse 30 (wie in mot2).

- 31034

CylinderAxis30

3D-Druck getestet

## Use
```
use <../Elements/CylinderAxis30.scad>
```

## Syntax
```
CylinderAxis30();

space = getCylinderAxis30Space();
```

## Rückgabewert getCylinderAxis30Space
Fläche als \[x,y]-Liste.
