proggi64/fischertechnik-box-foundation/Documentation/de/Elements/CylinderWheel23.md

# CylinderWheel23

Rad 23 mit Radachse. 

- 35586
- 36581

Das Rad muss auf die Radachse gesteckt werden. Der Baustein 5 der Radachse wird in den Zylinder der Halterung gesteckt. Siehe fischertechnik Baukasten 50.

CylinderWheel23

3D-Druck getestet

## Use
```
use <../Elements/CylinderWheel23.scad>
```

## Syntax
```
CylinderWheel23();

space = getCylinderWheel23Space();
```

## Rückgabewert getCylinderWheel23Space
Benötigte Fläche als \[x,y]-Liste.
