proggi64/fischertechnik-box-foundation/Documentation/de/Elements/CylinderInternalGearWheel.md

# CylinderInternalGearWheel
Innenzahnrad.
- 35694

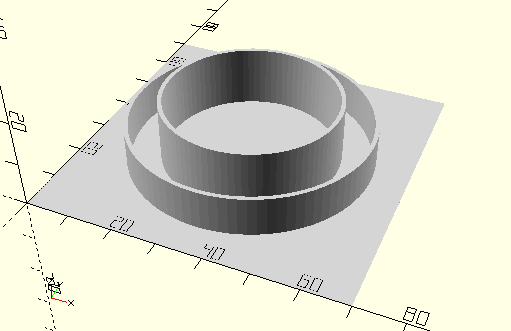
[picture p96: Documentation/images/CylinderInternalGearwheel.png]
CylinderInternalGearWheel


## Use
```
use <../Elements/CylinderInternalGearWheel.scad>
```

## Syntax
```
CylinderInternalGearWheel();

space = getCylinderInternalGearWheelSpace();
```

## Rückgabewert getCylinderInternalGearWheelSpace
Fläche als \[x,y]-Liste
