proggi64/fischertechnik-box-foundation/Documentation/de/Elements/CylinderTire20.md

# CylinderTire20

1-4 Reifen 20 (neuere Version ohne Zacken innen).

- 31017

CylinderTire20

## Use
```
use <../Elements/CylinderTire20.scad>
```

## Syntax
```
CylinderTire20(
    count=3);

space = getCylinderTire20Space(
    count=3);
```

| Parameter | Typ | Beschreibung |
| --- | --- | --- |
| count | Integer | Anzahl der Reifen, die auf dem Halter gestapelt werden. Bis drei Reifen verändert die Gesamthöhe nicht, sondern nur die des Absatzes unten am Zylinder. Bei vier hat der Zylinder keinen Absatz mehr und ist hoch genug für die vier gestapelten Reifen. Höhere Zahlen sind nicht sinnvoll, da der Zylinder zu hoch für den Sortierkasten wird. |

## Rückgabewert getCylinderTire20Space
Grundfläche als \[x,y]-Liste.

## Beispiele
Test/Elements/TestCylinderTire20.scad

### Alle vier erlaubten Werte für count

<pre>code>use <../../Base/Placement.scad>
use <../../Base/Deployment.scad>
use <../../Elements/CylinderTire20.scad>

include <../../Base/PlacementOptions.scad>

CylinderTire20();

Place(40, 0)
    CylinderTire20(1);

Place(80, 0)
    CylinderTire20(2);

Place(120, 0)
    CylinderTire20(3);

Place(160, 0)
    CylinderTire20(4);
</pre></code>

TestCylinderTire20
