proggi64/fischertechnik-box-foundation/Documentation/de/Elements/FrameTwoConnectors15.md

# FrameTwoConnectors15
Zwei Verbinder 15.
- 31060

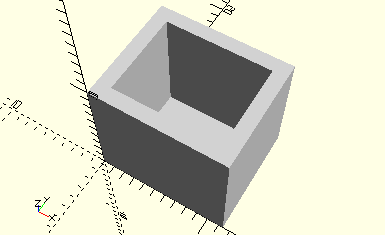
[picture p101: Documentation/images/FrameTwoConnectors15.png]
FrameTwoConnectors15


Die zwei Verbinder 15 werden senkrecht nebeneinander in den Rahmen gesteckt.

## Use
```
use <../Elements/FrameTwoConnectors15.scad>
```

## Syntax
```
FrameTwoConnectors15();

space = getFrameTwoConnectors15Space();
```

## Rückgabewert getFrameTwoConnectors15Space
Fläche als \[x,y]-Liste
