proggi64/fischertechnik-box-foundation/Documentation/de/Elements/FrameLockingRing.md

# FrameLockingRing
Klemmring für Seiltrommel.
- 31020

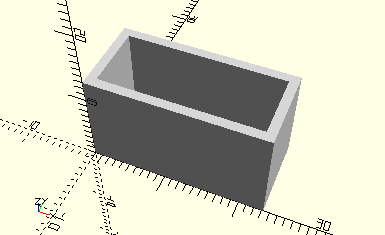
[picture p107: Documentation/images/FrameLockingRing.png]
FrameLockingRing


## Use
```
use <../Elements/FrameLockingRing.scad>
```

## Syntax
```
FrameLockingRing();

space = getFrameLockingRingSpace();
```

## Rückgabewert getFrameLockingRingSpace
Fläche als \[x,y]-Liste
