proggi64/fischertechnik-box-foundation/Documentation/de/Elements/FrameMotor6V.md

# FrameMotor6V
Gleichstrommotor 6V.
- 31039

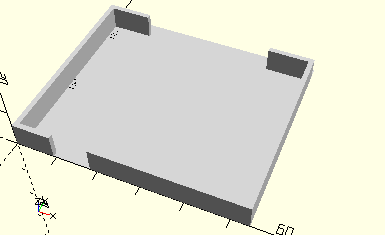
[picture p108: Documentation/images/FrameMotor6V.png]
FrameMotor6V


Die Aussparung unten ist für die untere Steckbuche, so dass das Kabel auch im Sortierkasten gesteckt bleiben kann. Das Element ist identisch mit mot1.

## Use
```
use <../Elements/FrameMotor6V.scad>
```

## Syntax
```
FrameMotor6V();

space = getFrameMotor6VSpace();
```

## Rückgabewert getFrameMotor6VSpace
Fläche als \[x,y]-Liste
