proggi64/fischertechnik-box-foundation/Documentation/de/Elements/FramePhotoResistor30.md

# FramePhotoResistor30
Fotowiderstand 30.
- 31361

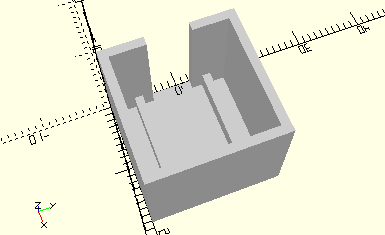
[picture p109: Documentation/images/FramePhotoResistor30.png]
FramePhotoResistor30


Der Widerstand wird aufrecht in den Rahmen gestellt.

## Use
```
use <../Elements/FramePhotoResistor30.scad>
```

## Syntax
```
FramePhotoResistor30();

space = getFramePhotoResistor30Space();
```

## Rückgabewert getFramePhotoResistor30Space
Fläche als \[x,y]-Liste
