proggi64/fischertechnik-box-foundation/Documentation/de/Elements/FramePlaneMirror.md

# FramePlaneMirror
Planspiegel 15 x 30.
- 31368

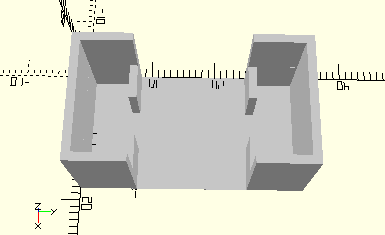
[picture p110: Documentation/images/FramePlaneMirror.png]
FramePlaneMirror


## Use
```
use <../Elements/FramePlaneMirror.scad>
```

## Syntax
```
FramePlaneMirror();

space = getFramePlaneMirrorSpace();
```

## Rückgabewert getFramePlaneMirrorSpace
Fläche als \[x,y]-Liste
