proggi64/fischertechnik-box-foundation/Documentation/de/Elements/FramePluggedCapacitor.md

# FramePluggedCapacitor
Kondensator 100 nF mit 2 Steckern.
- 36387

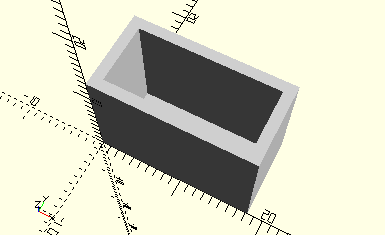
[picture p111: Documentation/images/FramePluggedCapacitor.png]
FramePluggedCapacitor


Es werden die beiden Stecker in den Rahmen gesteckt. Vergleiche ec2.

## Use
```
use <../Elements/FramePluggedCapacitor.scad>
```

## Syntax
```
FramePluggedCapacitor();

space = getFramePluggedCapacitorSpace();
```

## Rückgabewert getFramePluggedCapacitorSpace
Fläche als \[x,y]-Liste
