proggi64/fischertechnik-box-foundation/Documentation/de/Elements/FramePluggedResistor.md

# FramePluggedResistor
Widerstand 22 kOhm mit 2 Steckern.
- 36381

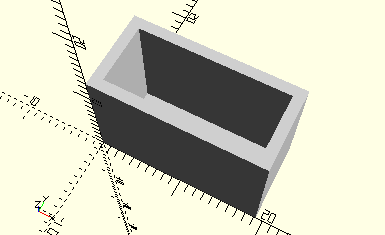
[picture p112: Documentation/images/FramePluggedResistor.png]
FramePluggedResistor


Es werden die beiden Stecker in den Rahmen gesteckt. Vergeliche ec2.

## Use
```
use <../Elements/FramePluggedResistor.scad>
```

## Syntax
```
FramePluggedResistor();

space = getFramePluggedResistorSpace();
```

## Rückgabewert getFramePluggedResistorSpace
Fläche als \[x,y]-Liste
