proggi64/fischertechnik-box-foundation/Documentation/de/Elements/FramePulley.md

# FramePulley
Seilrolle 21.
- 35795
- 35797

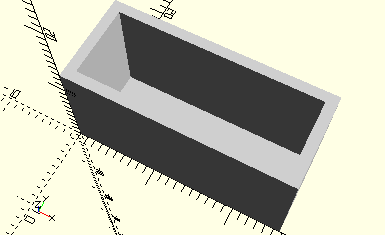
[picture p113: Documentation/images/FramePulley.png]
FramePulley


## Use
```
use <../Elements/FramePulley.scad>
```

## Syntax
```
FramePulley();

space = getFramePulleySpace();
```

## Rückgabewert getFramePulleySpace
Fläche als \[x,y]-Liste
