proggi64/fischertechnik-box-foundation/Documentation/de/Elements/FramePushButton.md

# FramePushButton
Taster oder Polwendeschalter.
- 31331
- 31332

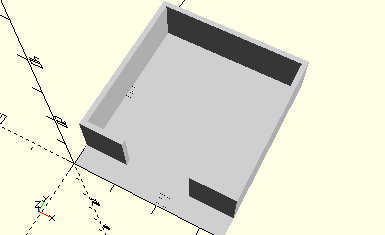
[picture p114: Documentation/images/FramePushButton.png]
FramePushButton


## Use
```
use <../Elements/FramePushButton.scad>
```

## Syntax
```
FramePushButton();

space = getFramePushButtonSpace();
```

## Rückgabewert getFramePushButtonSpace
Fläche als \[x,y]-Liste
