proggi64/fischertechnik-box-foundation/Documentation/de/Elements/FrameShortHook.md

# FrameShortHook
Seilhaken kurz.
- 38224
- 38225

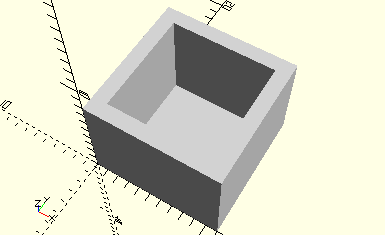
[picture p115: Documentation/images/FrameShortHook.png]
FrameShortHook


## Use
```
use <../Elements/FrameShortHook.scad>
```

## Syntax
```
FrameShortHook();

space = getFrameShortHookSpace();
```

## Rückgabewert getFrameShortHookSpace
Fläche als \[x,y]-Liste
