proggi64/fischertechnik-box-foundation/Documentation/de/Elements/FrameGearBox.md

# FrameGearBox
Stufengetriebe für 6V-Motor.
- 31048

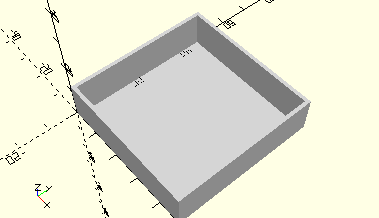
[picture p121: Documentation/images/FrameGearBox.png]
FrameGearBox


## Use
```
use <../Elements/FrameGearBox.scad>
```

## Syntax
```
FrameGearBox();

space = getFrameGearBoxSpace();
```

## Rückgabewert getFrameGearBoxSpace
Fläche als \[x,y]-Liste
