proggi64/fischertechnik-box-foundation/Documentation/de/Elements/FrameDriversCabLeftRight.md

# FrameDriversCabLeftRight
Linker und rechter Teil Führerhaus.
- 38435
- 38436

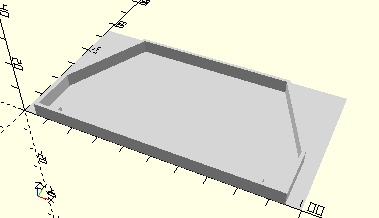
[picture p122: Documentation/images/FrameDriversCabLeftRight.png]
FrameDriversCabLeftRight


## Use
```
use <../Elements/FrameDriversCabLeftRight.scad>
```

## Syntax
```
FrameDriversCabLeftRight();

space = getFrameDriversCabLeftRightSpace();
```

## Rückgabewert getFrameDriversCabLeftRightSpace
Fläche als \[x,y]-Liste
