proggi64/fischertechnik-box-foundation/Documentation/de/Elements/FrameBracketWithAxle80.md

# FrameBracketWithAxle80
Getriebehalter mit Welle 180.
- 38201

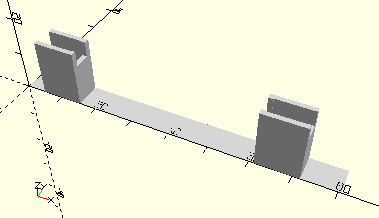
[picture p123: Documentation/images/FrameBracketWithAxle80.png]
FrameBracketWithAxle80


## Use
```
use <../Elements/FrameBracketWithAxle80.scad>
```

## Syntax
```
FrameBracketWithAxle80();

space = getFrameBracketWithAxle80Space();
```

## Rückgabewert getFrameBracketWithAxle80Space
Fläche als \[x,y]-Liste
