proggi64/fischertechnik-box-foundation/Documentation/de/Elements/FrameCouplingBracket.md

# FrameCouplingBracket
Lagerbock.
- 38252

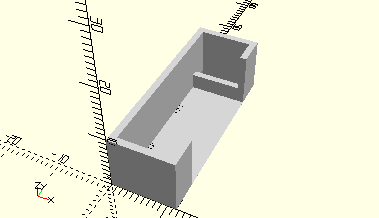
[picture p124: Documentation/images/FrameCouplingBracket.png]
FrameCouplingBracket


## Use
```
use <../Elements/FrameCouplingBracket.scad>
```

## Syntax
```
FrameCouplingBracket();

space = getFrameCouplingBracketSpace();
```

## Rückgabewert getFrameCouplingBracketSpace
Fläche als \[x,y]-Liste
