proggi64/fischertechnik-box-foundation/Documentation/de/Elements/FrameBracketWithoutWorm.md

# FrameBracketWithoutWorm
Lager ohne Schnecke für den 6V-Motor.
- 31046

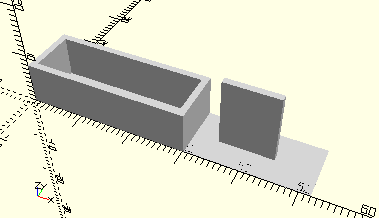
[picture p126: Documentation/images/FrameBracketWithoutWorm.png]
FrameBracketWithoutWorm


## Use
```
use <../Elements/FrameBracketWithoutWorm.scad>
```

## Syntax
```
FrameBracketWithoutWorm();

space = getFrameBracketWithoutWormSpace();
```

## Rückgabewert getFrameBracketWithoutWormSpace
Fläche als \[x,y]-Liste
