proggi64/fischertechnik-box-foundation/Documentation/de/Elements/FrameBracketWithWorm.md

# FrameBracketWithWorm
Lager mit Schnecke für den 6V-Motor.
- 31045

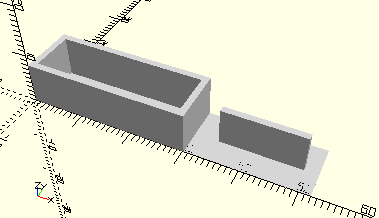
[picture p127: Documentation/images/FrameBracketWithWorm.png]
FrameBracketWithWorm


## Use
```
use <../Elements/FrameBracketWithWorm.scad>
```

## Syntax
```
FrameBracketWithWorm();

space = getFrameBracketWithWormSpace();
```

## Rückgabewert getFrameBracketWithWormSpace
Fläche als \[x,y]-Liste
