proggi64/fischertechnik-box-foundation/Documentation/de/Elements/FrameAperture.md

# FrameAperture
Loch-, Schlitz- oder Kreuzblende.
- 31371
- 31372
- 31373

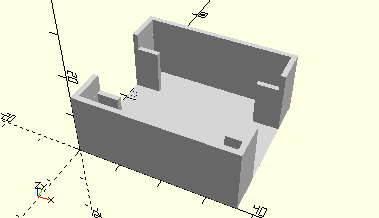
[picture p128: Documentation/images/FrameAperture.png]
FrameAperture


## Use
```
use <../Elements/FrameAperture.scad>
```

## Syntax
```
FrameAperture();

space = getFrameApertureSpace();
```

## Rückgabewert getFrameApertureSpace
Fläche als \[x,y]-Liste
