proggi64/fischertechnik-box-foundation/Documentation/de/Elements/FrameAxis60Open.md

# FrameAxis60Open
Achse 60.
- 31032

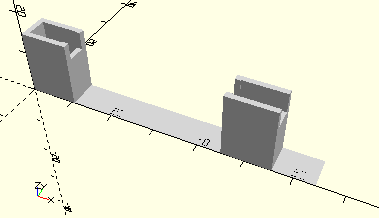
[picture p129: Documentation/images/FrameAxis60Open.png]
FrameAxis60Open


Der Rahmen ist offen, so dass z.B. eine längere Achse eingelegt werden kann. Siehe Kasten mot1.

## Use
```
use <../Elements/FrameAxis60Open.scad>
```

## Syntax
```
FrameAxis60Open();

space = getFrameAxis60OpenSpace();
```

## Rückgabewert getFrameAxis60OpenSpace
Fläche als \[x,y]-Liste
