proggi64/fischertechnik-box-foundation/Documentation/de/Elements/CylinderGearZ20.md

# CylinderGearZ20
Zahnrad Z20.
- 31021

CylinderGearZ20

## Use
```
use <../Elements/CylinderGearZ20.scad>
```

## Syntax
```
CylinderGearZ20();

space = getCylinderGearZ20Space();
```

## Rückgabewert getCylinderGearZ20Space
Fläche als \[x,y]-Liste
