proggi64/fischertechnik-box-foundation/Documentation/de/Elements/CylinderHubWithZ30.md

# CylinderHubWithZ30

Nabe mit Zahrad Z30.

- 31014
- 36264

CylinderHubWithZ30

## Use
```
use <../Elements/CylinderHubWithZ30.scad>
```

## Syntax
```
CylinderHubWithZ30();

space = getCylinderHubWithZ30Space();
```

## Rückgabewert getCylinderHubWithZ30Space
Fläche als \[x,y]-Liste. Diese Fläche ist größer als die des fast identischen Moduls [CylinderHub](CylinderHub.md), da hier noch der Umfang des Z30 berücksichtigt wird.
