proggi64/fischertechnik-box-foundation/Documentation/de/Elements/FrameAngleIsosceles.md

# FrameAngleIsosceles

Winkelstein 30 gleichschenklig.

- 31011

## Use
```
use <../Elements/FrameAngleIsosceles.scad>
```

## Syntax
```
FrameAngleIsosceles(
    count=1);

space = getFrameAngleIsoscelesSpace()
    count=1);
```

| Parameter | Typ | Beschreibung |
| --- | --- | --- |
| count | Integer | Anzahl der Bausteine nebeneinander (X-Richtung). |

## Rückgabewert getFrameAngleIsoscelesSpace
Äußere Fläche des Rahmens als \[x,y]-Liste.
