proggi64/fischertechnik-box-foundation/Documentation/de/Elements/FrameHingedBlock.md

# FrameHingedBlock

Gerade liegender Gelenkstein.

- 31008
- 35831

FrameHingedBlock

## Use
```
use <../Elements/FrameHingedBlock.scad>
```

## Syntax
```
FrameHingedBlock();

space = getFrameHingedBlockSpace();
```

## Rückgabewert getFrameHingedBlockSpace
Äußere Fläche als \[x,y]-Liste.
