proggi64/fischertechnik-box-foundation/Documentation/de/Elements/RailsBasePlate180x90.md

# RailsBasePlate180x90

Grundplatte 180 x 90 mm.

- 31001

RailsBasePlate180x90

## Use
```
use <../Elements/RailsBasePlate180x90.scad>
```

## Syntax
```
RailsBasePlate180x90();

space = getRailsBasePlate180x90Space();
```

## Rückgabewert getRailsBasePlate180x90Space
Grundfläche als \[x,y]-Liste.
