proggi64/fischertechnik-box-foundation/Documentation/de/Elements/RailsBasePlate90x90.md

# RailsBasePlate90x90

Grundplatte 90 x 90 mm.

- 31002

RailsBasePlate90x90

## Use
```
use <../Elements/RailsBasePlate90x90.scad>
```

## Syntax
```
RailsBasePlate90x90();

space = getRailsBasePlate90x90Space();
```

## Rückgabewert getRailsBasePlate90x90Space
Grundfläche als \[x,y]-Liste.
