proggi64/fischertechnik-box-foundation/Documentation/de/Elements/CylinderAndAxisDiscCam.md

# CylinderAndAxisDiscCam

Halterung für Nockenscheibe.

- 31038
- 35466

CylinderAndAxisDiscCam

## Use
<pre><code>use &lt;../Elements/CylinderAndAxisDiscCam.scad&gt;</pre></code>

## Syntax
```
CylinderAndAxisDiscCam();

space = getCylinderAndAxisDiscCamSpace();
```

## Rückgabewert getCylinderAndAxisDiscCamSpace
Fläche als \[x,y]-Liste.
