proggi64/fischertechnik-box-foundation/Documentation/de/ModelBase/getFrameBracketSpace.md

# getFrameBracketSpace

Funktion: Liefert die Fläche für eine Halterung eines Getriebeaufsatzes.

__getFrameBracketSpace__ liefert die Fläche der von [__FrameBracket__](FrameBracket.md) erzeugten Elemente.

## Use
```
use <../ModelBase/Complex.scad>
```

## Syntax
```
getFrameBracketSpace();
```

## Rückgabewert
Außenfläche eines von [__FrameBracket__](FrameBracket.md) erzeugten Elements als \[x,y]-Liste, inkl. des Bereichs für die Achse bzw. Schnecke.
