proggi64/fischertechnik-box-foundation/Documentation/de/ModelBase/getFrameRackSpace.md

# getFrameRackSpace

Funktion: Liefert die Fläche eines Rahmens für Zahnstangen.

Es wird die Fläche geliefert, die von [__FrameRack__](FrameRack.md) erzeugt wird.

## Use
```
use <../ModelBase/Complex.scad>
```

## Syntax
```
getFrameRackSpace();
```

## Rückgabewert
Außenfläche eines von [__FrameRack__](FrameRack.md) erzeugten Elements als \[x,y]-Liste.
