proggi64/fischertechnik-box-foundation/Documentation/de/ModelBase/getDockableEdgedFrameDepth.md

# getDockableEdgedFrameDepth

Funktion: Liefert den zusätzlichen Abstand eines oben oder unten angedockten Rahmens, wenn dieser über __DockableEdgedFrame__ erzeugt wird. Der Abstand wird zur Wand eingehalten und zusätzlich werden zwei Stege eingefügt, die mit der Außenwand verschmelzen.

ComplexTestDockableEdgedFrame

## Use
```
use <../ModelBase/Complex.scad>
include <../Base/PlacementOptions.scad>
```

## Syntax
```
getDockableEdgedFrameDepth(
  edgeDistance, 
  alignY=NoAlign);
```

| Parameter | Typ | Beschreibung |
| --- | --- | --- |
| edgeDistance | Decimal | Zusätzliche Distanz des Rahmens zur Wand, falls an die linke oder rechte Wand angedockt werden soll. |
| alignY | Integer (Enum) | __NoAlign__, falls nicht angedockt werden soll. Dann wird 0 zurückgeliefert. Sonst __AlignBottom__ oder __AlignTop__. |

## Rückgabewert
Zusätzliche Distanz des Rahmens zur Wand, an die gedckt wird. Der Wert ist 0, wenn für *alignX* __NoAlign__ übergeben wird.
