proggi64/fischertechnik-box-foundation/Documentation/de/ModelBase/getDockableEdgedFrameWidth.md

# getDockableEdgedFrameWidth

Funktion: Liefert den zusätzlichen Abstand eines links oder rechts angedockten Rahmens, wenn dieser über __DockableEdgedFrame__ erzeugt wird. Der Abstand wird zur Wand eingehalten und zusätzlich werden zwei Stege eingefügt, die mit der Außenwand verschmelzen.

ComplexTestDockableEdgedFrame

## Use
```
use <../ModelBase/Complex.scad>
include <../Base/PlacementOptions.scad>
```

## Syntax
```
getDockableEdgedFrameWidth(
  edgeDistance, 
  alignX=NoAlign);
```

| Parameter | Typ | Beschreibung |
| --- | --- | --- |
| edgeDistance | Decimal | Zusätzliche Distanz des Rahmens zur Wand, falls an die linke oder rechte Wand angedckt werden soll. |
| alignX | Integer (Enum) | __NoAlign__, falls nicht angedockt werden soll. Dann wird 0 zurückgeliefert. Sonst __AlignLeft__ oder __AlignRight__. |

## Rückgabewert
Zusätzliche Distanz des Rahmens zur Wand, an die gedckt wird. Der Wert ist 0, wenn für *alignX* __NoAlign__ übergeben wird.
