proggi64/fischertechnik-box-foundation/Documentation/de/Base/getFragments.md

# getFragments

Funktion: Liefert die Anzahl der Fragmente für __cylinder__-Objekte ($fn). 

Die Funktion wird durchgängig in der gesamten Bibliothek eingesetzt. Der Betrag ist so bemessen, dass runde Oberflächen entstehen.

## Use
```
use <../Base/Constants.scad>
```

## Syntax
```
getFragments();
```

## Rückgabewert
Anzahl der Fragmente, die bei Zylindern intern verwendet werden. Die Funktion wird intern durchgängig eingesetzt.
