proggi64/fischertechnik-box-foundation/Documentation/de/Base/getBox190Space.md

# getBox190Space

Funktion: Liefert die nutzbare Fläche eines Fischertechnik Sortierkastens 190 x 130. Die Box wird mit dem Modul [__Box190__](Box190.md) importiert.

## Use
```
use <../Base/Boxes.scad>
```

## Syntax
```
getBox190Space();
```

## Rückgabewert
x/y-Wertpaar (\[x, y\]), welche die Breite und Tiefe der Innenfläche enthält. Die Fläche ist etwas kleiner als 190 x 130 mm.
