proggi64/fischertechnik-box-foundation/Documentation/de/Base/getBox130Space.md

# getBox130Space

Funktion: Liefert die nutzbare Fläche eines Fischertechnik Sortierkastens 130 x 95. Die Box wird mit dem Modul [__Box130__](Box130.md) importiert.

## Use
```
use <../Base/Boxes.scad>
```

## Syntax
```
getBox130Space();
```

## Rückgabewert
x/y-Wertpaar (\[x, y\]), welche die Breite und Tiefe der Innenfläche enthält. Die Fläche ist etwas kleiner als 130 x 95 mm.
