proggi64/fischertechnik-box-foundation/Documentation/de/Base/getAxisDiameter.md

# getAxisDiameter

Funktion: Liefert den Durchmesser einer Fischertechnik Achse (4mm).

## Use
```
use <../Base/Constants.scad>
```

## Syntax
```
getAxisDiameter();
```

## Rückgabewert
Konstanter Wert 4 für den Durchmesser einer Achse in mm.
