proggi64/fischertechnik-box-foundation/Documentation/de/Elements/AxisLockingGear10.md

# AxisLockingGear10
Rastzahnrad 10 (stehend).
- 35945

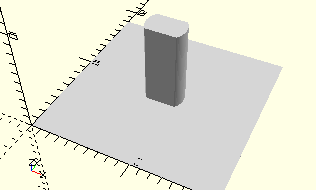
[picture p135: Documentation/images/AxisLockingGear10.png]
AxisLockingGear10


3D-Druck getestet.

## Use
```
use <../Elements/AxisLockingGear10.scad>
```

## Syntax
```
AxisLockingGear10();

space = getAxisLockingGear10Space();
```

## Rückgabewert getAxisLockingGear10Space
Fläche als \[x,y]-Liste
