proggi64/fischertechnik-box-foundation/Documentation/de/Elements/AxisLockingWorm.md

# AxisLockingWorm
Rastschnecke (stehend).
- 35072

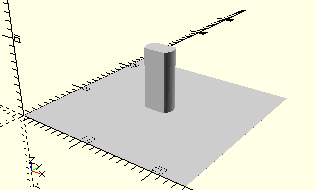
[picture p136: Documentation/images/AxisLockingWorm.png]
AxisLockingWorm


3D-Druck getestet

## Use
```
use <../Elements/AxisLockingWorm.scad>
```

## Syntax
```
AxisLockingWorm();

space = getAxisLockingWormSpace();
```

## Rückgabewert getAxisLockingWormSpace
Fläche als \[x,y]-Liste
