proggi64/fischertechnik-box-foundation/Documentation/de/Elements/ComboLockingWinchDrumAndHolder.md

# ComboLockingWinchDrumAndHolder
Rastseilwinde 30 montiert mit Halterung.
- 35069
- 35070

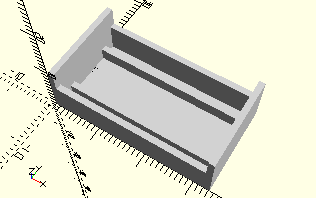
[picture p137: Documentation/images/ComboLockingWinchDrumAndHolder.png]
ComboLockingWinchDrumAndHolder


3D-Druck getestet.

## Use
```
use <../Elements/ComboLockingWinchDrumAndHolder.scad>
```

## Syntax
```
ComboLockingWinchDrumAndHolder();

space = getComboLockingWinchDrumAndHolderSpace();
```

## Rückgabewert getComboLockingWinchDrumAndHolderSpace
Fläche als \[x,y]-Liste
