proggi64/fischertechnik-box-foundation/Documentation/de/Elements/AxisLockingPulley12.md

# AxisLockingPulley12
Rastseilrolle 12.
- 136775

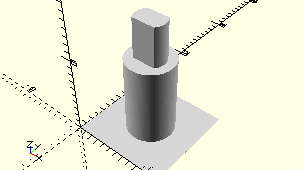
[picture p138: Documentation/images/AxisLockingPulley12.png]
AxisLockingPulley12


## Use
```
use <../Elements/AxisLockingPulley12.scad>
```

## Syntax
```
AxisLockingPulley12();

space = getAxisLockingPulley12Space();
```

## Rückgabewert getAxisLockingPulley12Space
Fläche als \[x,y]-Liste
