proggi64/fischertechnik-box-foundation/Documentation/de/Elements/AxisLockingCrank.md

# AxisLockingCrank
Rastkurbel.
- 35088

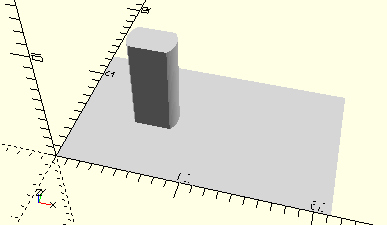
[picture p139: Documentation/images/AxisLockingCrank.png]
AxisLockingCrank


## Use
```
use <../Elements/AxisLockingCrank.scad>
```

## Syntax
```
AxisLockingCrank();

space = getAxisLockingCrankSpace();
```

## Rückgabewert getAxisLockingCrankSpace
Fläche als \[x,y]-Liste
