proggi64/fischertechnik-box-foundation/Documentation/de/Base/Merge.md

# Merge

Fügt die angegebene Anzahl von Kopien des Children-Elements so aneinander, dass dessen Trennwände zu jeweils einer verschmelzen. __Merge__ ist vor allem sinnvoll für das Aneinanderfügen von Elementen, die durch Trennwände eingerahmt sind. Durch die freie Angabe des *dividerThickness*-Parameters können aber auch beliebige andere Elemente ineinander geschoben werden.

## Use
```
use <../Base/Deployment.scad>
include <../Base/PlacementOptions.scad>
```

## Syntax
```
Merge(
  count,
  space, 
  rotation=NoRotation, 
  dividerThickness = getDividerThickness())
  {children}
```

| Parameter | Typ | Beschreibung |
| --- | --- | --- |
| count | Integer | Anzahl der Kopien des child, die aneinander gefügt werden sollen. |
| space | \[x,y] | Fläche, welche das children-Element einnimmt. Hierfür kann die jeweilige __get*ElementName*Space()__-Funktion als Wert übergeben werden. |
| rotation | Integer (Enum) | Gibt für das Children-Element an, wie es vor dem Verteilen gedreht werden soll. Mögliche Werte sind __Rotate0__, __Rotate90__, __Rotate180__ und __Rotate270__. Die Drehung wird für jedes erzeugte Element angewandt. Die Liste kann ganz weggelassen werden, dann gelten für alle Elemente __NoRotation__. Ist die Liste unvollständig, wird für die restlichen Elemente __NoRotation__ angenommen. |
| dividerThickness | Decimal | Wandstärke des Children-Elements. Standardwert ist die Standardwandstärke von [__getDividerThickness__](getDividerThickness.md). |

## Beispiel
```
use <../../Base/Deployment.scad>
use <../../ModelBase/Simple.scad>

include <../../Base/PlacementOptions.scad>

space = [30, 15, 5];
volume = getFrameOuterVolume(space);

Merge(3, volume, Rotate0)
    Frame(space);
```

Merge
