proggi64/fischertechnik-box-foundation/Documentation/de/Elements/AxisLockingAxisCoupling.md

# AxisLockingAxisCoupling
Rastachsenkupplung stehend.
- 35073

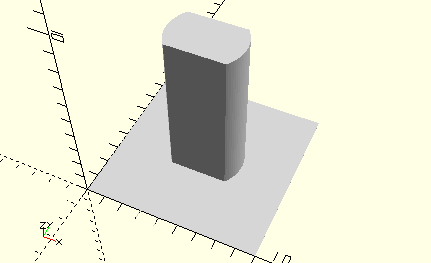
[picture p140: Documentation/images/AxisLockingAxisCoupling.png]
AxisLockingAxisCoupling


## Use
```
use <../Elements/AxisLockingAxisCoupling.scad>
```

## Syntax
```
AxisLockingAxisCoupling();

space = getAxisLockingAxisCouplingSpace();
```

## Rückgabewert getAxisLockingAxisCouplingSpace
Fläche als \[x,y]-Liste
