proggi64/fischertechnik-box-foundation/Documentation/de/Base/getAxisLockingLength.md

# getAxisLockingLength

Funktion: Liefert die jeweilige Länge des Rastbereichs einer Rastachse an den beiden Enden.

## Use
```
use <../Base/Constants.scad>
```

## Syntax
```
getAxisLockingLength();
```

## Rückgabewert
Konstanter Wert 8,0 für den Rastbereich einer Rastachse in mm.
