proggi64/fischertechnik-box-foundation/Documentation/de/Elements/ComboWormAndNutScrew.md

# ComboWormAndNutScrew
Antriebsschnecke mit Mutter montiert (liegend).
- 31915
- 37438

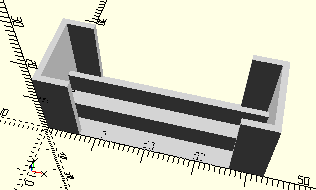
[picture p141: Documentation/images/ComboWormAndNutScrew.png]
ComboWormAndNutScrew


## Use
```
use <../Elements/ComboWormAndNutScrew.scad>
```

## Syntax
```
ComboWormAndNutScrew();

space = getComboWormAndNutScrewSpace();
```

## Rückgabewert getComboWormAndNutScrewSpace
Fläche als \[x,y]-Liste
