proggi64/fischertechnik-box-foundation/Documentation/de/Elements/HolderGearSupportWithWorm.md

# HolderGearSupportWithWorm
Getriebehalter mit Schnecke m 0,5 für Mini-Motor (mini-mot 1).
- 31069

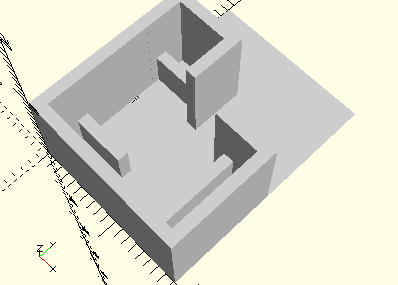
[picture p142: Documentation/images/HolderGearSupportWithWorm.png]
HolderGearSupportWithWorm


## Use
```
use <../Elements/HolderGearSupportWithWorm.scad>
```

## Syntax
```
HolderGearSupportWithWorm();

space = getHolderGearSupportWithWormSpace();
```

## Rückgabewert getHolderGearSupportWithWormSpace
Fläche als \[x,y]-Liste
