proggi64/fischertechnik-box-foundation/Documentation/de/ModelBase/getDockableEdgedFrameSpace.md

# getDockableEdgedFrameSpace

Funktion: Liefert die Fläche für einen mit [__DockableEdgedFrame__](DockableEdgedFrame.md) erzeugten Rahmen. Der Platz für die in die Wand hineinragenden optionalen Stege wird nicht mit eingerechnet.

ComplexTestDockableEdgedFrame

## Use
```
use <../ModelBase/Complex.scad>
include <../Base/PlacementOptions.scad>
```

## Syntax
```
getDockableEdgedFrameSpace(
  volume, 
  alignX=NoAlign,
  alignY=NoAlign,
  edgeDistance=getStandardEdgeDistance());
```

| Parameter | Typ | Beschreibung |
| --- | --- | --- |
| alignX | Integer (Enum) |  __NoAlign__, falls nicht links oder rechts angedockt werden soll. Sonst __AlignLeft__ oder __AlignRight__. |
| alignY | Integer (Enum) |  __NoAlign__, falls nicht oben oder unten angedockt werden soll. Sonst __AlignBottom__ oder __AlignTop__. |
| edgeDistance | Decimal | Zusätzliche Distanz des Rahmens zur der Wand, an die angedockt werden soll. |

## Rückgabewert
Gesamte Fläche, die der Rahmen innerhalb des nutzbaren Bereichs des Sortierkastens benötigt. Die Teile der optionalen Stege und Rahmenwände, die in die Außenwand ragen, werden nicht mit eingerechnet.
