proggi64/fischertechnik-box-foundation/Documentation/de/Elements/AxisFlatHubWithGearZ40.md

# AxisFlatHubWithGearZ40
Zahnrad Z40 mit Flachnabe.
- 31015
- 31022

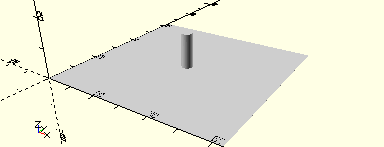
[picture p149: Documentation/images/AxisFlatHubWithGearZ40.png]
AxisFlatHubWithGearZ40


Nur in Verbindung mit einer Flachnabe, die auf die Achse gesteckt wird. Die Seite mit den drei Abstandshaltern am Zahnrad Z40 muss unten sein, wie im Kasten 50/2.

## Use
```
use <../Elements/AxisFlatHubWithGearZ40.scad>
```

## Syntax
```
AxisFlatHubWithGearZ40();

space = getAxisFlatHubWithGearZ40Space();
```

## Rückgabewert getAxisFlatHubWithGearZ40Space
Fläche als \[x,y]-Liste
