proggi64/fischertechnik-box-foundation/Documentation/de/Elements/AxisPulley.md

# AxisPulley
Seilrolle.
- 35795

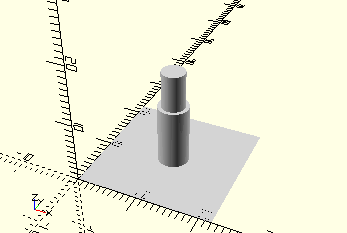
[picture p151: Documentation/images/AxisPulley.png]
AxisPulley


Achse zum Aufstecken einer Seilrolle wie im Baukasten 50/1.

## Use
```
use <../Elements/AxisPulley.scad>
```

## Syntax
```
AxisPulley();

space = getAxisPulleySpace();
```

## Rückgabewert getAxisPulleySpace
Fläche als \[x,y]-Liste
