proggi64/fischertechnik-box-foundation/Documentation/de/Elements/ComboInnerGearWheelAndIdlerGearZ15.md

# ComboInnerGearWheelAndIdlerGearZ15
Kombination für Innenzahnrad und Zahrad Z15.
- 35694
- 35695

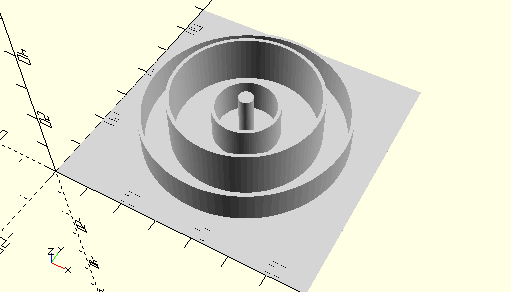
[picture p154: Documentation/images/ComboInnerGearWheelAndIdlerGearZ15.png]
ComboInnerGearWheelAndIdlerGearWheelZ15


## Use
```
use <../Elements/ComboInnerGearWheelAndIdlerGearZ15.scad>
```

## Syntax
```
ComboInnerGearWheelAndIdlerGearZ15();

space = getComboInnerGearWheelAndIdlerGearZ15Space();
```

## Rückgabewert getComboInnerGearWheelAndIdlerGearZ15Space
Fläche als \[x,y]-Liste
