proggi64/fischertechnik-box-foundation/Documentation/de/Elements/ComboHolderWinchDrumWithLockingRings.md

# ComboHolderWinchDrumWithLockingRings
Seiltrommel mit zwei Klemmringen.
- 31016
- 31020

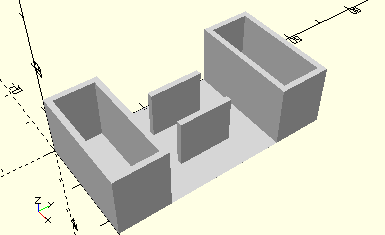
[picture p155: Documentation/images/ComboHolderWinchDrumWithLockingRings.png]
ComboHolderWinchDrumWithLockingRings


## Use
```
use <../Elements/ComboHolderWinchDrumWithLockingRings.scad>
```

## Syntax
```
ComboHolderWinchDrumWithLockingRings();

space = getComboHolderWinchDrumWithLockingRingsSpace();
```

## Rückgabewert getComboHolderWinchDrumWithLockingRingsSpace
Fläche als \[x,y]-Liste
