proggi64/fischertechnik-box-foundation/Documentation/de/Elements/HolderLinkBeam.md

# HolderLinkBeam
Lenkbalken.
- 38418

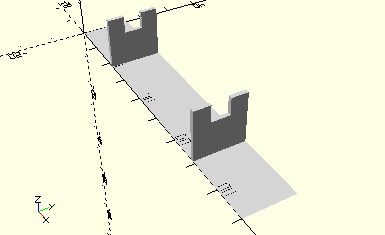
[picture p156: Documentation/images/HolderLinkBeam.png]
HolderLinkBeam


## Use
```
use <../Elements/HolderLinkBeam.scad>
```

## Syntax
```
HolderLinkBeam();

space = getHolderLinkBeamSpace();
```

## Rückgabewert getHolderLinkBeamSpace
Fläche als \[x,y]-Liste
