proggi64/fischertechnik-box-foundation/Documentation/de/Elements/HolderWinchDrum.md

# HolderWinchDrum
Seiltrommel.
- 31016

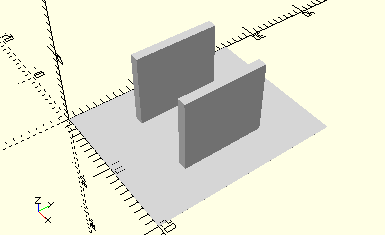
[picture p157: Documentation/images/HolderWinchDrum.png]
HolderWinchDrum


## Use
```
use <../Elements/HolderWinchDrum.scad>
```

## Syntax
```
HolderWinchDrum();

space = getHolderWinchDrumSpace();
```

## Rückgabewert getHolderWinchDrumSpace
Fläche als \[x,y]-Liste
