proggi64/fischertechnik-box-foundation/Documentation/de/Elements/HolderBulbLamp.md

# HolderBulbLamp
Kugelstecklampe oder Linsenstecklampe.
- 37869
- 37875

Halterung für einzelne Stecklampe.

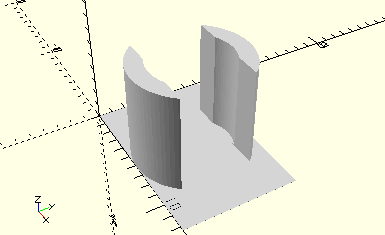
[picture p158: Documentation/images/HolderBulbLamp.png]
HolderBulbLamp


## Use
```
use <../Elements/HolderBulbLamp.scad>
```

## Syntax
```
HolderBulbLamp();

space = getHolderBulbLampSpace();
```

## Rückgabewert getHolderBulbLampSpace
Fläche als \[x,y]-Liste
