proggi64/fischertechnik-box-foundation/Documentation/de/Elements/AxisIdlerGearZ15.md

# AxisIdlerGearZ15
Zahnrad Z15.

- 35695

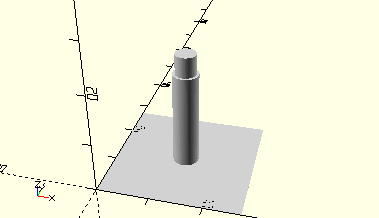
[picture p163: Documentation/images/AxisIdlerGearZ15.png]
AxisIdlerGearZ15


## Use
```
use <../Elements/AxisIdlerGearZ15.scad>
```

## Syntax
```
AxisIdlerGearZ15();

space = getAxisIdlerGearZ15Space();
```

## Rückgabewert getAxisIdlerGearZ15Space
Fläche als \[x,y]-Liste
