proggi64/fischertechnik-box-foundation/Documentation/de/Base/Box130.md

# Box130

Erzeugt einen leeren fischertechnik Sortierkasten 130 x 95 mm mit Seitenwänden. Die Kästen sind mit den Originalen stapelbar.

BoxesTestBox130

Die Abbildung zeigt die gelb dargestellte Box 130 im Vergleich zur rot-transparent dargestellten Box 190. Um 90° gedreht passen zwei Boxen 130 gestapelt auf die Box 190. Sortierkästen in dieser kleinen Größe gab und gibt es von Fischertechnik nicht. In einen Sortierkasten 1000 passen 16 dieser Kästen.

__Box130__ dient als Grundlage für alle kompletten Eigenentwürfe von Sortierkästen in dieser Größe. Die Elemente werden hier platziert. Der Kasten ist so ausgerichtet, dass die Position 0,0 in der linken unteren Ecke des nutzbaren Bereichs liegt. Alle Elemente sind so definiert, dass sie sich um den Betrag, den die Funktion [__getExcess__](getExcess.md) liefert, in den Boden des Kastens senken.

Die Ausrichtungsfunktion des Moduls [__Place__](Place.md) verwendet als Standardwert der Fläche die nutzbare Grundfläche der [__Box190__](Box190.md). Um sie für __Box130__ aufzurufen, muss [__getBox130Space__](getBox130Space.md) für den Parameter *boxSpace* übergeben werden.

Elemente, die Docking unterstützen (z.B. [__FrameElectronicBlock__](../Elements/FrameElectronicBlock.md)) sind so entworfen, dass sie sich teilweise in die Seitenwand transparent integrieren, d.h. dass sie an den gedockten Seitenwänden in diese etwas hineinragen. Dadurch verschmilzt das Element mit der Außenwand.

## Use
```
use <../Base/Boxes.scad>
```

## Syntax
``
Box130();
```
