proggi64/fischertechnik-box-foundation/Documentation/de/Base/Box190.md

# Box190

Erzeugt einen leeren fischertechnik Sortierkasten 190 x 130 mm mit Seitenwänden. Die Kästen sind mit den Originalen stapelbar. __Box190__ entspricht der Größe der mit der Box 1000 gelieferten Sortierkästen und kann mit diesen gestapelt werden.

BoxesTestBox190

__Box190__ dient als Grundlage für alle kompletten Eigenentwürfe von Sortierkästen. Die Elemente werden hier platziert. Der Kasten ist so ausgerichtet, dass die Position 0,0 in der linken unteren Ecke des nutzbaren Bereichs liegt. Alle Elemente sind so definiert, dass sie sich um den Betrag, den die Funktion [__getExcess__](getExcess.md) liefert, in den Boden des Kastens senken.

Box190_0_0

Die Ausrichtungsfunktion des Moduls [__Place__](Place.md) verwendet als Standardwert der Fläche die nutzbare Grundfläche der __Box190__.

Elemente, die Docking unterstützen (z.B. [__FrameElectronicBlock__](FrameElectronicBlock.md)) sind so entworfen, dass sie sich teilweise in die Seitenwand transparent integrieren, d.h. dass sie an den gedockten Seitenwänden in diese etwas hineinragen. Dadurch verschmilzt das Element mit der Außenwand.

## Use
```
use <../Base/Boxes.scad>
```

## Syntax
```
Box190();
```
