proggi64/fischertechnik-box-foundation/Documentation/de/Base/getBoxInnerHeight.md

# getBoxInnerHeight

Funktion: Liefert die Höhe des Innenraums der fischertechnik Sortierbox. Dies ist die Höhe vom Boden bis zum oberen Rand.

## Use
```
use <../Base/Boxes.scad>
```

## Syntax
```
getBoxInnerHeight();
```

## Rückgabewert
Höhe des Sortierkastens abzüglich der Stärke des Bodens.
