proggi64/fischertechnik-box-foundation/Documentation/de/ModelBase/getFrameOuterVolume.md

# getFrameOuterVolume

Funktion: Liefert das äußere Volumen ("bounding box") eines Rahmens.

Angegeben muss dafür das Volumen des Bauteils. Die zurückgelieferten X- und Y-Werte enthalten die Toleranz und die Wandstärken.

## Use
```
use <../ModelBase/Complex.scad>
include <../Base/PlacementOptions.scad>
```

## Syntax
```
getFrameOuterVolume(
  volume, 
  tolerance=getTolerance());
```

| Parameter | Typ | Beschreibung |
| --- | --- | --- |
| volume | \[x,y,z] | Volumen des Bauteils, das im Rahmen Platz haben soll. Ausnahme: Die Höhe in *volume.z* entspricht der Höhe des Rahmens und nicht des Bauteils. |
| tolerance | Decimal | Toleranz, die im Rahmen verwendet werden soll. Standard ist [__getTolerance__](../Base/getTolerance.md). Um diesen Betrag wird das innere Volumen in X- und Y-Richtung vergrößert, damit das Bauteil nach dem Druck hineinpasst. In manchen Spezialfällen soll der Rahmen um keinen Toleranzbetrag vergrößert werden, dann muss hier 0 angegeben werden. |

## Rückgabewert
Liefert das äußere Volumen des Rahmens in einer \[x,y,z]-Liste.
