proggi64/fischertechnik-box-foundation/Documentation/de/ModelBase/getFrameAxisSpace.md

# getFrameAxisSpace

Funktion: Liefert die Fläche einer mit __FrameAxis__ erzeugten Achshalterung.

TestFrameAxis50

## Use
```
use <../ModelBase/Complex.scad>
```

## Syntax
```
getFrameAxisSpace(
  length);
```

| Parameter | Typ | Beschreibung |
| --- | --- | --- |
| length | Decimal | Länge der Achse, für welche die Achshalterung erzeugt wird. |

## Rückgabewert
Liste mit den errechneten X-, Y- und Z-Werten. Der Z-Wert (die Höhe) ist die Höhe der Halterungen.
