proggi64/fischertechnik-box-foundation/Documentation/de/Base/getTubeWallThickness.md

# getTubeWallThickness

Funktion: Liefert Stärke der Wände eines Element-Zylinders.

SimpleTestTube

Die Wände von Zylindern sind etwas schmäler als die normaler Trennwände. Das Basis-Modul [__Tube__](../ModelBase/Tube.md) verwendet die Funktion.

## Use
```
use <../Base/Constants.scad>
```

## Syntax
```
getTubeWallThickness();
```

## Rückgabewert
Standardwert für die Stärke der Zylinderwände. Dies ist ein um einen kleinen Faktor verringerter Wert von [__getDividerThickness__](getDividerThickness.md).
