proggi64/fischertechnik-box-foundation/Documentation/de/Base/getStandardWebDistance.md

# getStandardWebDistance

Funktion: Liefert den Abstand eines Stegs zur jeweiligen Ecke eines andockbaren Elements.

EdgedFrame

Im Bild ist dies der Abstand der beiden gelben Stege an der linken Ecke zur Ecke. Das Basis-Modul [__DockableEdgedFrame__](../ModelBase/DockableEdgedFrame.md) setzt die Funktion ein.

## Use
```
use <../Base/Constants.scad>
```

## Syntax
```
getStandardWebDistance();
```

## Rückgabewert
Abstand eines generierten Stegs bei [__DockableEdgedFrame__](../ModelBase/DockableEdgedFrame.md) zur Ecke der Nutzfläche des Elements. Dieser Abstand wird von der Ecke zum Rand des Stegs gemessen, der zur Ecke zugewandt ist. In ec1 bis ec3 ist dieser Abstand z.B. 15 mm, was auch hier als Standardwert definiert wurde.
