proggi64/fischertechnik-box-foundation/Documentation/de/Base/getStandardEdgeDistance.md

# getStandardEdgeDistance

Funktion: Liefert den Standard-Abstand für andockbare Rahmen mit Stegen ([__DockableEdgedFrame__](../ModelBase/DockableEdgedFrame.md)).

EdgedFrame

Wenn eine Seite über die Align-Parameter an eine Wand angedockt sein soll, ist __getStandardEdgeDistance()__ der Abstand der normalen Element-Fläche von der Wand. Diese Funktion wird durchgängig in der Bibliothek für die Funktionalität verwendet. Das Basis-Modul [__DockableEdgedFrame__](../ModelBase/DockableEdgedFrame.md) setzt die Funktion ein.

## Use
```
use <../Base/Constants.scad>
```

## Syntax
```
getStandardEdgeDistance();
```

## Rückgabewert
Länge der Stege in mm, die beim Andocken eines [__DockableEdgedFrame__](../ModelBase/DockableEdgedFrame.md) generiert werden. Dies entspricht dem Abstand der Nutzfläche des Rahmens von der Wand des Sortierkastens.
