proggi64/fischertechnik-box-foundation/Documentation/de/Base/getBoxWebWidth.md

# getBoxWebWidth

Funktion: Liefert die Standardlänge eines Stegs eines fischertechnik Sortierkastens. Die Stege sind auf der Höhe, die [__getBoxUsageHeight__](getBoxUsageHeight.md) liefert und unterstützen das Stapeln von Sortierkästen aufeinander. Sie ragen um den Betrag, den __getBoxWebWidth__ liefert, in den Inneraum der Box hinen. Sie können mit dem Modul [__BoxWeb__](BoxWeb.md) erzeugt werden.

BoxesTestBoxWeb01

## Use
```
use <../Base/Boxes.scad>
```

## Syntax
```
getBoxWebWidth();
```

## Rückgabewert
Betrag in mm, um den ein Steg von der oberen Seitenwand in den nutzbaren Bereich des Sortierkastens hineinragt. Der Wert wird als Standardwert verwendet, wenn bei [__BoxWeb__](BoxWeb.md) kein abweichender Betrag angegeben wird. Durch die schräge Seitenwand verringert sich dieser Betrag nach unten zum Boden hin.
