proggi64/fischertechnik-box-foundation/Documentation/de/Base/getBoxWallThickness.md

# getBoxWallThickness

Funktion: Liefert die Stärke der Außenwände der fischertechnik Sortierbox.

## Use
```
use <../Base/Boxes.scad>
```

## Syntax
```
getBoxWallThickness();
```

## Rückgabewert
Stärke der Außenwand eines Fischertechnik-Sortierkastens in mm. Dies ist der Betrag, um den der Sortierkasten am Ursprung in negative X- und Y-Richtung verschoben wird, damit die Nutzfläche den Ursprung 0, 0 hat.
