proggi64/fischertechnik-box-foundation/Original Building Kits/ec/ec1_inlay.stl

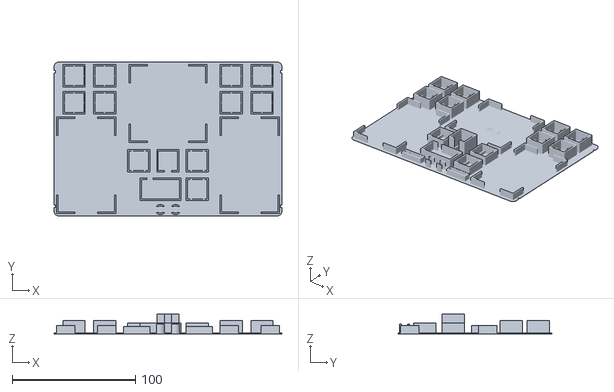
[picture p172: CAD file, 2022-06-18]
Original Building Kits/ec/ec1_inlay.stl
184.7 x 124.7 x 15.8
