proggi64/fischertechnik-box-foundation/Building Kits/hobby/h4 MF.stl

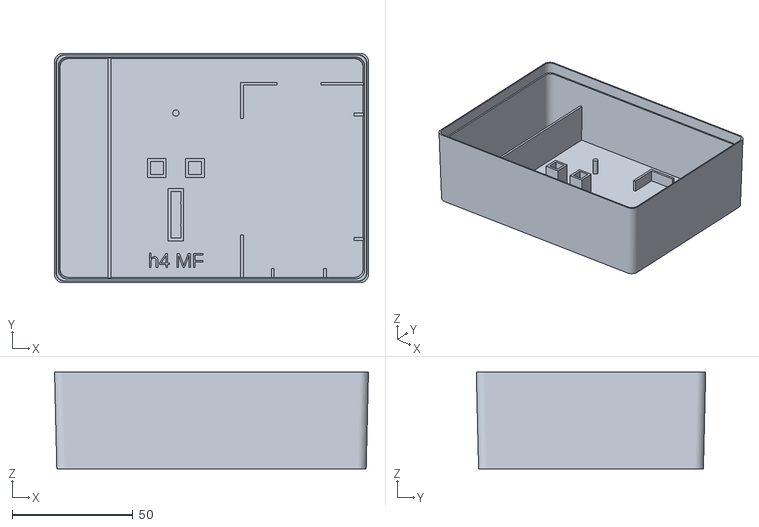
[picture p173: CAD file, 2022-08-04]
Building Kits/hobby/h4 MF.stl
130.0 x 95.0 x 40.0
