proggi64/fischertechnik-box-foundation/Building Kits/hobby/hl1 PB.stl

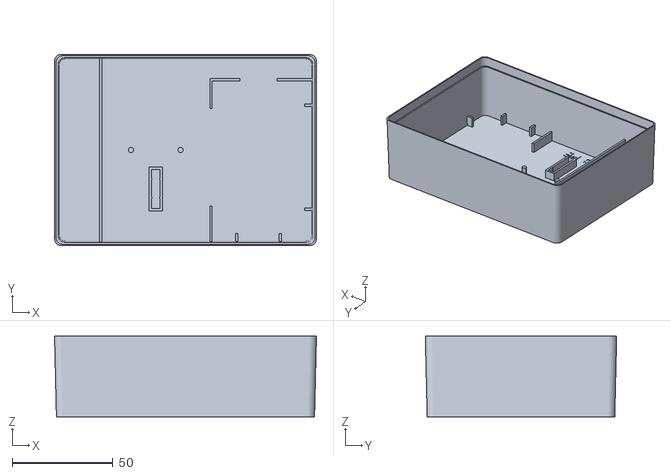
[picture p174: CAD file, 2022-08-04]
Building Kits/hobby/hl1 PB.stl
130.0 x 95.0 x 40.0
